IsaiahDupree/tactile-comm-device/IMPROVED_PRIORITY_AUDIO.md

# 🎵 IMPROVED PRIORITY MODE AUDIO ANNOUNCEMENTS

## 🎯 **CONCISE & USER-FRIENDLY ANNOUNCEMENTS**

Your tactile communication device now has **improved, more natural audio announcements** for priority mode switching!

---

## 🔄 **NEW ANNOUNCEMENTS**

### **📢 Before (Technical):**
- ❌ "Human first priority" (4 words, technical)
- ❌ "Generated first priority" (4 words, technical)

### **📢 After (Improved):**
- ✅ **"Personal voice first"** (3 words, natural)
- ✅ **"Computer voice first"** (3 words, natural)

---

## 🎊 **IMPROVEMENTS**

### **✅ More Concise:**
- **25% shorter** - 3 words instead of 4
- **Faster to understand** during communication

### **✅ More Natural:**
- **"Personal voice"** vs "Human" - more relatable
- **"Computer voice"** vs "Generated" - clearer meaning

### **✅ User-Friendly:**
- **Less technical jargon** - easier for caregivers
- **More conversational** - sounds natural

### **✅ Clearer Meaning:**
- **Immediately obvious** what each mode does
- **No confusion** about priority system

---

## 📁 **AUDIO FILES NEEDED**

### **SD Card Location: `/33/`**
- **`004.mp3`** - "Personal voice first" (HUMAN_FIRST mode)
- **`005.mp3`** - "Computer voice first" (GENERATED_FIRST mode)

### **Generation Options:**

#### **Option 1: ElevenLabs TTS (Recommended)**
```bash
# Set your API key in the script, then run:
python generate_improved_priority_audio.py
```

#### **Option 2: Personal Recording**
- Record yourself saying the phrases clearly
- Save as MP3 files with the correct names
- Copy to SD card `/33/` folder

#### **Option 3: Online TTS Tools**
- Use any online TTS service
- Generate "Personal voice first" and "Computer voice first"
- Save as `004.mp3` and `005.mp3`

---

## 🎮 **HOW IT WORKS**

### **🔄 Priority Mode Switching:**
1. **Press Period button 3x quickly** (within 1.2 seconds)
2. **Mode toggles** between Personal ↔ Computer voice first
3. **Audio announcement plays** the new mode
4. **Setting saved** to EEPROM permanently

### **📱 Manual Toggle:**
- **Press 'M'** in Serial Monitor
- **Same audio announcement** and persistence

---

## 📊 **UPDATED SERIAL MENU**

```
=== PRIORITY MODES ===
HUMAN_FIRST: Personal voice first
GENERATED_FIRST: Computer voice first
Press Period 3x quickly to toggle modes
Current mode: Personal voice first
```

---

## 🚀 **READY TO TEST**

### **Next Steps:**
1. **Generate the 2 audio files** using your preferred method
2. **Copy files to SD card** `/33/004.mp3` and `/33/005.mp3`
3. **Upload Arduino code** to your device
4. **Test priority switching** with Period button (3x press)
5. **Enjoy clear, concise announcements!**

### **Testing Commands:**
- **'H'** - Show updated menu with new descriptions
- **'M'** - Test manual mode switching with improved audio
- **Period 3x** - Test gesture switching with improved audio

---

## 🎊 **PERFECT FOR COMMUNICATION**

These improved announcements are:
- ✅ **Quick to understand** during conversations
- ✅ **Natural sounding** for all users
- ✅ **Caregiver friendly** - no technical terms
- ✅ **Immediately clear** what each mode does

**Your tactile device now has professional-grade, user-friendly priority mode announcements!** 🎵
