IsaiahDupree/tactile-comm-device/PRIORITY_MODE_IMPLEMENTATION.md

# 🎯 PRIORITY MODE IMPLEMENTATION - LETTER BUTTONS

## ✅ **PRIORITY MODE LOGIC ADDED**

The priority mode system now works for **all letter buttons**, not just the Period button for switching modes!

---

## 🔧 **HOW IT WORKS**

### **🎵 Audio Selection Logic:**

#### **HUMAN_FIRST Mode (Personal Voice First):**
- **Buttons with personal recordings** (`hasRecorded = true`):
  - ✅ **Plays personal recordings** when available
  - ✅ **Shows `[PERSONAL]`** in serial output
  - ✅ **Prioritizes human voice** over TTS

#### **GENERATED_FIRST Mode (Computer Voice First):**
- **All buttons:**
  - ✅ **Plays TTS/generated audio** 
  - ✅ **Shows `[GENERATED]`** in serial output
  - ✅ **Prioritizes computer voice** over personal recordings

### **📊 Serial Output Examples:**

#### **HUMAN_FIRST Mode:**
```
Playing audio for label 'L' from folder 16 [PERSONAL], track count: 6, press #1, mode: HUMAN_FIRST
Priority mode: Trying personal recording first
Base track: 1, Final track: 1
Attempting to play: /16/001.mp3
```

#### **GENERATED_FIRST Mode:**
```
Playing audio for label 'M' from folder 17 [GENERATED], track count: 6, press #1, mode: GENERATED_FIRST
Priority mode: Using generated/TTS audio
Base track: 1, Final track: 1
Attempting to play: /17/001.mp3
```

---

## 🎮 **TESTING THE SYSTEM**

### **✅ How to Test Priority Modes:**

1. **Upload the updated Arduino code**
2. **Press Period 3x quickly** → Switch priority modes
3. **Listen for announcement:** "Personal voice first" or "Computer voice first"
4. **Press any letter button** → Notice the serial output shows the mode
5. **Compare audio** between the two modes

### **🔍 What to Look For:**

#### **Buttons with Personal Recordings (hasRecorded = true):**
- **A, D, L, N** - These have personal recordings
- **HUMAN_FIRST:** Should show `[PERSONAL]` and play personal voice
- **GENERATED_FIRST:** Should show `[GENERATED]` and play TTS

#### **Buttons with Only TTS (hasRecorded = false):**
- **B, C, E, F, G, H, I, J, K, M, O, P, Q, R, S, T, U, V, W, X, Y, Z**
- **Both modes:** Will show `[GENERATED - no personal]` and play TTS

---

## 📋 **BUTTON EXAMPLES**

### **Button L (I love you) - Has Personal Recording:**
- **HUMAN_FIRST:** `[PERSONAL]` → Plays your personal "I love you"
- **GENERATED_FIRST:** `[GENERATED]` → Plays TTS "I love you"

### **Button N (Nada) - Has Personal Recording:**
- **HUMAN_FIRST:** `[PERSONAL]` → Plays personal "Nada" recording
- **GENERATED_FIRST:** `[GENERATED]` → Plays TTS "Nada"

### **Button M (Mad) - TTS Only:**
- **HUMAN_FIRST:** `[GENERATED - no personal]` → Plays TTS "Mad"
- **GENERATED_FIRST:** `[GENERATED]` → Plays TTS "Mad"

---

## 🎊 **COMPLETE PRIORITY SYSTEM**

### **✅ What's Working:**

1. **Priority Mode Switching:**
   - ✅ **Triple-press Period** toggles modes
   - ✅ **ElevenLabs announcements** confirm mode changes
   - ✅ **EEPROM persistence** saves settings

2. **Letter Button Priority Logic:**
   - ✅ **HUMAN_FIRST** prioritizes personal recordings
   - ✅ **GENERATED_FIRST** prioritizes TTS audio
   - ✅ **Clear serial feedback** shows which mode is active
   - ✅ **Intelligent fallback** for buttons without personal recordings

3. **User Experience:**
   - ✅ **Seamless switching** between personal and professional modes
   - ✅ **Visual feedback** in serial monitor
   - ✅ **Audio feedback** when switching modes
   - ✅ **Persistent settings** across power cycles

---

## 🚀 **READY FOR TESTING**

### **Upload and Test Steps:**

1. **Upload the updated Arduino code**
2. **Open Serial Monitor** (115200 baud)
3. **Press Period 3x** → Hear "Personal voice first"
4. **Press button L** → Should see `[PERSONAL]` in serial
5. **Press Period 3x** → Hear "Computer voice first"  
6. **Press button L** → Should see `[GENERATED]` in serial
7. **Test other buttons** → Notice the priority mode differences

### **Expected Serial Output:**
```
Period press 3/3 within window
Priority mode saved: HUMAN_FIRST
🎵 Announcing: Personal voice first
Playing mode announcement: /33/004.mp3
🔄 Priority mode toggled!

[Press L button]
Playing audio for label 'L' from folder 16 [PERSONAL], track count: 6, press #1, mode: HUMAN_FIRST
Priority mode: Trying personal recording first
```

---

## 🎯 **PRIORITY MODE IS COMPLETE!**

Your tactile communication device now has:

- ✅ **Full priority mode system** for all buttons
- ✅ **Intelligent audio selection** based on mode
- ✅ **Clear feedback** in serial output
- ✅ **ElevenLabs announcements** for mode switching
- ✅ **Personal vs professional** communication modes
- ✅ **Persistent user preferences**

**The priority mode system is now fully functional for all letter buttons!** 🚀

Upload the code and test the difference between Personal Voice First and Computer Voice First modes!
