IsaiahDupree/tactile-comm-device/PRIORITY_MODE_INTEGRATION_COMPLETE.md

# ✅ PRIORITY MODE INTEGRATION COMPLETE!

## 🎉 **TACTILE DEVICE FULLY ENHANCED**

Your tactile communication device now has **complete priority mode integration** with the existing codebase!

---

## ✅ **INTEGRATION COMPLETED**

### ✅ **Complete Integration:**

1. **🔧 EEPROM library added** for persistent storage
2. **🎯 Priority mode variables** added to global scope  
3. **🚀 loadPriorityMode()** integrated into existing setup()
4. **🔄 finalizePeriodWindow()** integrated into existing loop()
5. **🎮 Period triple-press detection** integrated into handlePress()
6. **📱 'M' command** added to existing serial handler
7. **📋 Priority mode info** added to existing printMenu()
8. **🎵 Audio playback functions** fixed to use existing VS1053 system

### **🎯 No Duplicate Functions:**
- ✅ **Used existing setup()** function - no duplication
- ✅ **Used existing loop()** function - no duplication  
- ✅ **Used existing handlePress()** function - enhanced
- ✅ **Used existing printMenu()** function - enhanced
- ✅ **Used existing serial commands** - added 'M' command

---

## 🎮 **HOW IT WORKS**

### **🔄 Priority Mode Switching:**
1. **Press Period button 3 times** within 1.2 seconds
2. **handlePress()** detects Period button and calls **handlePeriodPress()**
3. **Triple-press detection** counts presses within time window
4. **Mode toggles** between HUMAN_FIRST ↔ GENERATED_FIRST
5. **Audio announcement** plays the new mode
6. **EEPROM saves** the setting permanently

### **📱 Manual Mode Toggle:**
- **Press 'M'** in Serial Monitor to toggle modes manually
- **Same audio announcement** and EEPROM save as triple-press

### **💾 Persistent Storage:**
- **Mode saved** to EEPROM address 0
- **Loaded on startup** via loadPriorityMode() in setup()
- **Survives power cycles** and resets

---

## 🎵 **AUDIO SYSTEM**

### **🔊 Mode Announcements:**
- **`/33/004.mp3`** - "Human first priority" 
- **`/33/005.mp3`** - "Generated first priority"
- **Uses existing VS1053** audio playback system
- **Stops current audio** before playing announcement

### **🎧 Audio Priority Logic:**
- **HUMAN_FIRST:** Personal recordings → TTS fallback
- **GENERATED_FIRST:** TTS → Personal recordings fallback
- **Seamless integration** with existing audio mapping system

---

## 📊 **COMPLETE SYSTEM STATUS**

### **✅ Arduino Code Ready:**
- **120+ words** across all buttons
- **Priority mode system** fully integrated
- **No compilation errors** (except EEPROM.h lint in IDE)
- **Compatible with Arduino UNO R4 WiFi**

### **✅ SD Card Ready:**
- **84 TTS audio files** generated and copied
- **All folders 05-30** populated with expanded words
- **Existing personal recordings** preserved
- **SHIFT help system** ready for mode announcements

### **📝 Still Needed:**
- **2 mode announcement files:** `/33/004.mp3` and `/33/005.mp3`
- **16 personal recordings** for family names (optional)

---

## 🚀 **READY TO UPLOAD!**

### **Upload Process:**
1. **Connect Arduino UNO R4 WiFi** to computer
2. **Open Arduino IDE** and select board
3. **Upload tactile_communicator_vs1053.ino**
4. **Open Serial Monitor** (115200 baud)
5. **Test the system!**

### **Testing Steps:**
1. **Press 'H'** to see updated menu with priority modes
2. **Press 'M'** to test manual mode toggling
3. **Press Period 3x quickly** to test triple-press detection
4. **Press other buttons** to test normal operation
5. **Verify mode persists** after power cycle

---

## 📱 **SERIAL COMMANDS**

```
=== TACTILE COMMUNICATION DEVICE (VS1053) ===
C → Enter Calibration mode
E → Exit Calibration mode  
L → Load config from SD (config.csv)
S → Save config to SD (config.csv)
P → Print current mappings
M → Toggle priority mode manually
T → Test all buttons
+ → Volume up, - → Volume down, 1-9 → Set level
X → Stop current playback
H → Show this menu

=== PRIORITY MODES ===
HUMAN_FIRST: Personal recordings play first
GENERATED_FIRST: TTS audio plays first
Press Period 3x quickly to toggle modes
Current mode: HUMAN_FIRST

Press buttons to communicate!
```

---

## 🎊 **CONGRATULATIONS!**

Your tactile communication device now features:

- ✅ **120+ comprehensive vocabulary**
- ✅ **Dual priority modes** with smart switching
- ✅ **Triple-press gesture** for mode changes
- ✅ **Audio announcements** for feedback
- ✅ **Persistent settings** across power cycles
- ✅ **Professional integration** with existing code
- ✅ **No code duplication** or conflicts
- ✅ **Arduino UNO R4 WiFi ready**

**The integration is complete and ready for upload!** 🚀

Upload the code, generate the 2 mode announcement files, and enjoy your dramatically enhanced tactile communication system!
