IsaiahDupree/tactile-comm-device/PRIORITY_MODE_SYSTEM_ADDED.md

# ✅ PRIORITY MODE SYSTEM ADDED TO TACTILE DEVICE

## 🎉 **NEW FEATURE: DUAL PRIORITY MODES**

Your tactile communication device now has **two priority modes** that can be switched by pressing the **Period button 3 times quickly**!

---

## 🔄 **TWO PRIORITY MODES**

### **1. HUMAN_FIRST Mode (Default)**
- **Personal recordings** play first
- **TTS audio** plays as fallback
- **Best for familiar words** and personal expressions
- **Example:** "I love you" → Personal recording first, then TTS

### **2. GENERATED_FIRST Mode**  
- **TTS audio** plays first
- **Personal recordings** play as fallback
- **Best for consistent pronunciation** and new words
- **Example:** "Medicine" → TTS first, then personal recording

---

## 🎯 **HOW TO SWITCH MODES**

### **Triple-Press Period Button:**
1. **Press Period button 3 times** within 1.2 seconds
2. **Device announces** the new mode aloud
3. **Mode is saved** to EEPROM (survives power cycles)
4. **Normal Period function** still works with single/double press

### **Audio Announcements:**
- **"Human first priority"** - when switching to HUMAN_FIRST
- **"Generated first priority"** - when switching to GENERATED_FIRST

---

## 🛠️ **TECHNICAL IMPLEMENTATION**

### **Arduino Code Changes:**
- ✅ **EEPROM.h library** added for persistent storage
- ✅ **PriorityMode enum** with HUMAN_FIRST/GENERATED_FIRST
- ✅ **Triple-press detection** with 1.2-second window
- ✅ **Mode persistence** across power cycles
- ✅ **Audio announcements** for mode changes
- ✅ **Setup() integration** loads saved mode on startup
- ✅ **Loop() integration** handles period window finalization

### **New Functions Added:**
```cpp
void loadPriorityMode()        // Load mode from EEPROM
void savePriorityMode()        // Save mode to EEPROM  
void announcePriorityMode()    // Play mode announcement
void handlePeriodPress()       // Handle triple-press detection
void finalizePeriodWindow()    // Finalize single/double press
```

### **Audio Files Needed:**
- **`/33/004.mp3`** - "Human first priority" announcement
- **`/33/005.mp3`** - "Generated first priority" announcement

---

## 🎵 **AUDIO FILE LOCATIONS**

The priority mode announcements use the **SHIFT folder (33)** for system messages:

```
SD Card Structure:
/33/001.mp3 - Personal greeting (existing)
/33/002.mp3 - Device instructions (existing)  
/33/003.mp3 - Word mapping guide (existing)
/33/004.mp3 - "Human first priority" (NEW)
/33/005.mp3 - "Generated first priority" (NEW)
```

---

## 🚀 **USAGE SCENARIOS**

### **When to Use HUMAN_FIRST Mode:**
- ✅ **Family conversations** - personal names and expressions
- ✅ **Emotional communication** - "I love you", personal greetings
- ✅ **Familiar daily words** - names, personal preferences
- ✅ **When consistency with family voice is important**

### **When to Use GENERATED_FIRST Mode:**
- ✅ **Medical appointments** - consistent pronunciation of medications
- ✅ **Public settings** - clear, professional speech
- ✅ **New vocabulary** - words without personal recordings yet
- ✅ **When clarity and pronunciation are priority**

---

## 📱 **USER INTERFACE**

### **Serial Console Messages:**
```
🎉 System ready! Press buttons to communicate.
Current priority mode: HUMAN_FIRST
Press Period 3 times quickly to toggle priority mode.

Period press 1/3 within window
Period press 2/3 within window  
Period press 3/3 within window
🔄 Priority mode toggled!
Priority mode saved: GENERATED_FIRST
🎵 Announcing: Generated first priority
```

### **Status Indicators:**
- **Startup message** shows current mode
- **Console logging** for triple-press detection
- **Audio confirmation** when mode changes
- **EEPROM persistence** message on save/load

---

## 🎯 **NEXT STEPS TO COMPLETE**

### **1. Generate Audio Files**
- Record or generate "Human first priority" → `/33/004.mp3`
- Record or generate "Generated first priority" → `/33/005.mp3`

### **2. Copy to SD Card**
- Copy new audio files to SD card `/33/` folder
- Ensure existing SHIFT help files remain intact

### **3. Upload Arduino Code**
- Upload the updated `.ino` file with priority mode system
- Arduino UNO R4 WiFi fully compatible

### **4. Test the System**
- Test Period triple-press mode switching
- Verify audio announcements play correctly
- Test that normal Period function still works
- Confirm mode persists after power cycle

---

## 🎊 **CONGRATULATIONS!**

Your tactile communication device now has:
- ✅ **120+ words** across all buttons
- ✅ **Dual priority modes** for flexible communication
- ✅ **Smart mode switching** with triple-press gesture
- ✅ **Audio feedback** for mode changes
- ✅ **Persistent settings** that survive power cycles
- ✅ **Enhanced user experience** for different scenarios

**This makes your device incredibly versatile for both personal and professional communication needs!** 🚀
