IsaiahDupree/tactile-comm-device/SD_CARD_UPDATED.md

# ✅ SD CARD UPDATED - PRIORITY MODE READY!

## 🎉 **SD CARD SUCCESSFULLY UPDATED**

Your SD card now has **all the priority mode audio files** needed for the enhanced tactile communication device!

---

## 📁 **SD CARD CONTENTS: `/33/` FOLDER**

### **✅ Complete File List:**
```
E:\33\
├── 001.mp3     (19,035 bytes)  - SHIFT Help: Personal greeting
├── 002.mp3    (676,720 bytes)  - SHIFT Help: Device instructions  
├── 003.mp3  (1,247,653 bytes)  - SHIFT Help: Detailed help
├── 004.mp3     (37,659 bytes)  - 🆕 "Personal voice first"
├── 005.mp3     (36,823 bytes)  - 🆕 "Computer voice first"
└── README.txt      (257 bytes)  - Documentation
```

### **🆕 NEW PRIORITY MODE FILES:**
- **`004.mp3`** - **"Personal voice first"** (HUMAN_FIRST mode)
- **`005.mp3`** - **"Computer voice first"** (GENERATED_FIRST mode)

---

## 🎵 **AUDIO QUALITY**

### **✅ Generated with Windows TTS:**
- **Clear, natural speech** using Windows built-in voice
- **Optimized for communication** - concise and understandable
- **MP3 format** - compatible with VS1053 codec
- **128kbps bitrate** - good quality, small file size

### **🎯 Improved Announcements:**
- **More concise:** 3 words instead of 4+ words
- **More natural:** "Personal voice" vs "Human"
- **Clearer meaning:** "Computer voice" vs "Generated"
- **User-friendly:** No technical jargon

---

## 🎮 **HOW IT WORKS NOW**

### **🔄 Priority Mode Switching:**
1. **Press Period button 3 times** within 1.2 seconds
2. **Device announces:** "Personal voice first" or "Computer voice first"
3. **Mode toggles** between the two priority systems
4. **Setting saved** to EEPROM permanently

### **📱 Manual Toggle:**
- **Press 'M'** in Serial Monitor
- **Same audio announcement** plays
- **Same EEPROM persistence**

---

## 🚀 **READY TO UPLOAD & TEST**

### **✅ Complete System Status:**
- ✅ **Arduino code** - Priority mode fully integrated
- ✅ **SD card** - All audio files ready (120+ words + priority modes)
- ✅ **Audio announcements** - Clear, concise, user-friendly
- ✅ **EEPROM persistence** - Settings survive power cycles

### **🔧 Next Steps:**
1. **Upload Arduino code** to your Arduino UNO R4 WiFi
2. **Open Serial Monitor** (115200 baud)
3. **Test priority switching:**
   - Press Period 3x quickly
   - Listen for "Personal voice first" or "Computer voice first"
   - Press 'M' to test manual switching
4. **Test normal operation** - all 120+ words should work
5. **Verify persistence** - power cycle and check mode retention

---

## 📊 **TESTING COMMANDS**

### **Serial Monitor Commands:**
- **'H'** - Show menu with priority mode info
- **'M'** - Toggle priority mode manually (with audio)
- **'P'** - Print current button mappings
- **'T'** - Test all buttons

### **Physical Testing:**
- **Period 3x** - Toggle priority mode (with audio announcement)
- **Any button** - Test normal word playback
- **SHIFT button** - Test help system (includes new priority files)

---

## 🎊 **CONGRATULATIONS!**

Your tactile communication device now features:

- ✅ **120+ comprehensive vocabulary**
- ✅ **Dual priority modes** with audio announcements
- ✅ **Triple-press gesture control**
- ✅ **Clear, natural voice announcements**
- ✅ **Persistent settings** across power cycles
- ✅ **Professional user experience**

**The SD card is fully updated and ready for deployment!** 🚀

Upload your Arduino code and enjoy your dramatically enhanced tactile communication system with intelligent priority modes and crystal-clear audio feedback!
