IsaiahDupree/tactile-comm-device/TTS_UPDATE_COMPLETE_SUMMARY.md

# 🎵 TTS VOCABULARY UPDATE COMPLETE!

## ✅ **WHAT WE'VE ACCOMPLISHED:**

### **1. Console Logging Enhancement ✅**
- **Added `getAudioText()` function** to map audio files to their text content
- **Enhanced playback logging** to show exactly what words are being played
- **Example output:** `🎵 Playing: /23/002.mp3 -> "Sad"`

### **2. TTS Update Script Created ✅**
- **Complete vocabulary mapping** from your JSON specification
- **Smart personal recording detection** - won't overwrite Alari, Daddy, etc.
- **Voice ID configured:** `RILOU7YmBhvwJGDGjNmP` (previously used)
- **Ready to run** once you add your ElevenLabs API key

### **3. Audio Manifest Generated ✅**
- **Perfect track-to-text mapping** created at `E:\AUDIO_MANIFEST.json`
- **Shows exactly what each file contains:**
  - `/23/001.mp3` = "Susu" (personal recording)
  - `/23/002.mp3` = "Sad" (TTS)
  - `/23/003.mp3` = "Scarf" (TTS)
  - And so on...

### **4. Updated Arduino Code ✅**
- **Enhanced console logging** shows text content when playing audio
- **Two-bank priority system** fully supports your vocabulary
- **Smart bank selection** respects personal vs TTS priority

## 🎯 **EXPECTED CONSOLE OUTPUT:**

When you press the S button, you'll now see:
```
[BUTTON] PCF8575 #0 GPIO 7 → S [F:23/REC:1/TTS:7] | Press #1 @ 15234ms
Playing audio for label 'S' from folder 23 [REC:1/TTS:7], press #1, mode: HUMAN_FIRST
Priority mode: HUMAN_FIRST -> Selected RECORDED bank, track 1
🎵 Playing: /23/001.mp3 -> "Susu [REC]"
```

And for the second press:
```
🎵 Playing: /23/002.mp3 -> "Sad"
```

## 📋 **YOUR VOCABULARY MAPPING:**

**Personal Recordings (Protected):**
- A: Alari (`/05/001.mp3`)
- D: Daddy (`/08/001.mp3`)
- L: I love you (`/16/001.mp3`)
- N: Nada, Nadowie, Noah (`/18/001-003.mp3`)
- S: Susu (`/23/001.mp3`)

**TTS Words (Your JSON Vocabulary):**
- **A:** Amer, Apple, Arabic Show
- **B:** Bagel, Bathroom, Bed, Blanket, Breathe, Bye
- **C:** Call, Car, Chair, Coffee, Cold, Cucumber
- **D:** Deen, Doctor, Door, Down
- **F:** FaceTime, Funny
- **G:** Garage, Go, Good Morning
- **H:** Happy, Heartburn, Hot, How are you, Hungry
- **I:** Inside, iPad
- **K:** Kaiser, Kiyah, Kleenex, Kyan
- **L:** Lee, Light Down, Light Up
- **M:** Mad, Medical, Medicine, Meditate, Mohammad
- **N:** No
- **O:** Outside
- **P:** Pain, Phone
- **R:** Rest, Room
- **S:** Sad, Scarf, Shoes, Sinemet, Sleep, Socks, Stop
- **T:** TV, Togamet, Tylenol
- **U:** Up, Urgent Care
- **W:** Walk, Walker, Water, Wheelchair
- **Y:** Yes

## 🚀 **NEXT STEPS:**

### **To Generate TTS Files:**
1. **Add your ElevenLabs API key** to `update_vocabulary_tts.py`
2. **Run the script:** `python update_vocabulary_tts.py`
3. **Wait for generation** (~2-3 minutes for all files)

### **To Test Priority Mode:**
1. **Upload the updated Arduino code**
2. **Press S button once** → Should play "Susu" (personal) in HUMAN_FIRST mode
3. **Press S button twice** → Should play "Sad" (TTS)
4. **Triple-press Period** to switch modes
5. **Press S button once** → Should play "Sad" (TTS) in GENERATED_FIRST mode

## 🎵 **CONSOLE LOGGING BENEFITS:**

- **See exactly what's playing:** No more guessing which audio file is which
- **Debug priority mode:** Verify correct bank selection
- **Track personal recordings:** `[REC]` tag shows personal vs TTS
- **Troubleshoot issues:** Clear file path and content mapping

## ✅ **SYSTEM STATUS:**

- ✅ **SD Card:** Reorganized with proper REC/TTS banks
- ✅ **Arduino Code:** Enhanced with text logging and compilation fixes
- ✅ **Vocabulary:** Fully mapped to your JSON specification
- ✅ **TTS Script:** Ready to generate all missing audio files
- ✅ **Priority Mode:** Bulletproof two-bank system complete
- 🎯 **Ready for final testing!**

**Your tactile communication device now has comprehensive vocabulary support with crystal-clear console logging!** 🎯✨
