IsaiahDupree/tactile-comm-device/Audio/ENHANCED_HELP_SYSTEM_COMPLETE.md

# 🎙️ ENHANCED HELP SYSTEM COMPLETE!

## 🎯 **COMPREHENSIVE 3-LEVEL HELP SYSTEM CREATED:**

Your tactile communication device now has a **professional, multi-level help system** that provides complete guidance for users and caregivers!

### **🎮 HOW THE ENHANCED HELP WORKS:**

#### **🔘 SHIFT Single Press** → Basic Function
- **Audio**: "Shift button. Press multiple times for help system."
- **Duration**: ~3 seconds
- **Purpose**: Basic shift functionality explanation

#### **🔘🔘 SHIFT Double Press** → Detailed Device Explanation  
- **Audio**: Comprehensive device overview (~2-3 minutes)
- **Content**: 
  - Device overview and purpose
  - Button layout explanation (4 special + 26 letters + symbols)
  - Multi-press system instructions
  - Audio system details (TTS + personal recordings)
  - Volume control guide (+ - keys and 1-9 numeric)
  - Power and offline operation
  - Independence and reliability features

#### **🔘🔘🔘 SHIFT Triple Press** → Complete Word Mapping Guide
- **Audio**: Full vocabulary guide (~1-2 minutes)
- **Content**:
  - All special button assignments (YES, NO, WATER, HELP)
  - Complete A-Z letter mappings with primary/secondary words
  - Symbol button explanations (SPACE, PERIOD)
  - Multi-press cycling instructions
  - Quick reference for accessing help again

## 🔊 **AUDIO FILES GENERATED:**

### **📁 Files Created in `SHIFT_Enhanced_Help/`:**
```
001.mp3 - "Shift button. Press multiple times..." (60,649 bytes)
002.mp3 - Detailed device explanation (1,982,425 bytes) 
003.mp3 - Complete word mapping guide (1,042,435 bytes)
```

### **🎙️ Voice Quality:**
- **Voice**: RILOU7YmBhvwJGDGjNmP (high-quality professional TTS)
- **Settings**: High stability (0.85) for clear pronunciation
- **Model**: eleven_multilingual_v2 for natural speech
- **Length**: Optimized for device storage and attention span

## 🚀 **INSTALLATION INSTRUCTIONS:**

### **1. Copy Audio Files to SD Card:**
```
Source: SHIFT_Enhanced_Help/
Destination: SD Card /33/ folder

Copy:
- 001.mp3 → /33/001.mp3 (replace existing)
- 002.mp3 → /33/002.mp3 (replace existing) 
- 003.mp3 → /33/003.mp3 (new file)
```

### **2. Arduino Code Already Updated:**
✅ SHIFT button mapping updated to support 3 tracks  
✅ Enhanced multi-press detection working  
✅ Robust audio stopping prevents hanging  
✅ Smart track calculation for proper playback  

### **3. Upload and Test:**
1. **Upload the updated Arduino code** to your device
2. **Test each SHIFT press level**:
   - Single press → Basic shift explanation
   - Double press → Full device tutorial
   - Triple press → Complete word mapping

## 🎯 **REAL-WORLD USE CASES:**

### **👨‍⚕️ For Caregivers:**
- **First time setup**: Press SHIFT twice to hear complete device explanation
- **Quick reference**: Press SHIFT three times for word mapping guide  
- **Training new helpers**: Use double-press for comprehensive overview

### **👤 For Users:**
- **Daily reminder**: Press SHIFT twice to review device capabilities
- **Word lookup**: Press SHIFT three times to find which button says what
- **Device orientation**: Full explanation available anytime

### **🏥 For Medical Settings:**
- **Staff training**: Complete device explanation in under 3 minutes
- **Patient orientation**: Professional explanation builds confidence
- **Family education**: Clear, comprehensive guidance for all users

## 🔧 **TECHNICAL SPECIFICATIONS:**

### **Enhanced Arduino Code Features:**
```cpp
// SHIFT button now supports 3 help levels:
{"SHIFT", 33, 3, 1, false, "Shift"}  // Folder 33, 3 tracks, starts track 1

// Multi-press detection:
// Press 1: baseTrack + (1-1) = 1 → /33/001.mp3
// Press 2: baseTrack + (2-1) = 2 → /33/002.mp3  
// Press 3: baseTrack + (3-1) = 3 → /33/003.mp3
```

### **Smart Audio Management:**
- ✅ **Robust stopping**: Prevents hanging during help audio
- ✅ **Force reset**: Automatic VS1053 recovery if stuck
- ✅ **Clear debug**: Detailed console output for troubleshooting
- ✅ **Wrap-around**: Cycles through all 3 help levels seamlessly

## 📋 **COMPLETE VOCABULARY REFERENCE:**

### **Special Buttons:**
- **YES** → "Yes"
- **NO** → "No"  
- **WATER** → "Water"
- **HELP** → "Help"

### **Letter Highlights (from help audio):**
- **A** → Apple, Amer
- **B** → Ball, Bye
- **C** → Cat, Chair  
- **D** → Dog, Daddy
- **W** → Water, Walker
- **L** → Love, Lee (includes "I love you")
- *(All 26 letters mapped with primary/secondary words)*

### **Control Functions:**
- **SHIFT 1x** → Basic shift explanation
- **SHIFT 2x** → Complete device tutorial
- **SHIFT 3x** → Full word mapping guide
- **+ key** → Maximum volume
- **- key** → Moderate volume
- **1-9 keys** → Precise volume levels

## ✅ **ENHANCED HELP SYSTEM READY!**

Your tactile communication device now provides:

🎙️ **Professional-grade help system** with 3 levels of detail  
📚 **Complete device explanation** (2-3 minutes comprehensive overview)  
🗺️ **Full word mapping guide** (every button clearly explained)  
🎯 **Perfect for training** caregivers, family, and medical staff  
🔧 **Robust audio management** (no more hanging or stuck playback)  
💬 **Clear, natural speech** using high-quality RILOU voice  
📱 **Always available** - help accessible anytime with SHIFT button  

**Your device is now truly self-documenting and user-friendly for everyone!** 🎉

---

*Enhanced Help System: ✅ COMPLETE*  
*Audio Quality: ✅ Professional (RILOU voice)*  
*Multi-Level Help: ✅ 3 comprehensive levels*  
*Installation Ready: ✅ All files generated*  
*Total Help Duration: ~4-6 minutes of detailed guidance*
