IsaiahDupree/tactile-comm-device/Audio/FRESH_SD_CARD_COMPLETE.md

# Fresh SD Card Setup Complete! ✅

## NEW PRIORITY SYSTEM IMPLEMENTED

Your tactile communication device now has a **completely fresh SD card** with the **improved priority system**:

### 🎯 **New Priority System:**

1. **1st Press**: Generated TTS (clear, consistent, always available)
2. **2nd Press**: Personal Recorded Words (familiar voices, emotional connection)
3. **3rd+ Press**: Additional TTS words (extended vocabulary)

## 📁 **SD Card Structure Created**

✅ **57 TTS audio files generated** using ElevenLabs RILOU voice  
✅ **18 recorded words copied** to 2nd press positions  
✅ **Fresh folder structure** (01-33) with numbered files  
✅ **SHIFT help system** implemented  

## 🔧 **Arduino Code Updated**

The Arduino code now includes **detailed documentation** showing exactly what each button press will play:

```cpp
// A: 1=Apple[TTS], 2=Amer[REC], 3=Alari[REC], 4=Arabic[TTS], 5=Amory[REC]
{"A", 5, 5, true, "Apple"},

// B: 1=Ball[TTS], 2=Bye[REC], 3=Bathroom[TTS], 4=Bed[TTS]  
{"B", 6, 4, true, "Ball"},

// SHIFT with Help System: 1=Shift[TTS], 2=Device Help[TTS]
{"SHIFT", 33, 2, false, "Shift"}
```

## 🎙️ **SHIFT Double-Press Help System**

**Special Feature Implemented:** Press SHIFT twice quickly to hear:

> *"This is your tactile communication device. Press any button once for the main word, twice for personal recordings, or three times for additional options. Press SHIFT twice for help."*

## 📊 **Example Button Usage**

### Letter A:
- **Press 1**: "Apple" (TTS - clear, consistent)
- **Press 2**: "Amer" (Your recorded voice - personal, familiar)  
- **Press 3**: "Alari" (Your recorded voice)
- **Press 4**: "Arabic" (TTS)
- **Press 5**: "Amory" (Your recorded voice)

### Letter L:
- **Press 1**: "Love" (TTS)
- **Press 2**: "Lee" (Your recorded voice)
- **Press 3**: "I love you" (Your recorded voice) 
- **Press 4**: "Light" (TTS)

## ✅ **Ready for Testing**

1. **Upload the updated Arduino code** to your device
2. **Test the new priority system**:
   - Single press = TTS (always available)
   - Double press = Recorded words (personal touch)
3. **Test SHIFT double-press** for device help
4. **Enjoy the improved communication experience!**

## 🎵 **Audio Quality Summary**

- **Voice**: ElevenLabs RILOU (clear & understandable)
- **Total Files**: 57 TTS + 18 recorded = 75 audio files
- **File Format**: MP3, optimized for VS1053 codec
- **File Size**: Average 12-15KB per file
- **Multi-press Window**: 1000ms (1 second) for reliable detection

---

## 🚀 **Key Improvements from Fresh Setup**

### **✅ Better User Experience:**
- **Consistent first experience**: TTS always available on first press
- **Personal second experience**: Your voice for important words
- **Extended vocabulary**: Additional words on 3rd+ presses

### **✅ Clearer System Logic:**
- **Predictable**: Users know first press = TTS, second = personal
- **Documented**: Arduino code shows exactly what each press plays
- **Help system**: SHIFT double-press explains the device

### **✅ Technical Excellence:**
- **Clean slate**: Fresh SD card with proper structure
- **Proper naming**: Numbered files (001.mp3, 002.mp3, etc.)
- **Updated mappings**: Arduino code matches SD card exactly

---

**Your tactile communication device is now ready with the improved priority system! 🎉**

*Generated: 2025-08-01 20:52 EST*  
*SD Card: E:\ (Fresh Setup)*  
*Voice: RILOU (ElevenLabs)*  
*Priority: TTS First, Recorded Second*
