IsaiahDupree/tactile-comm-device/Audio/PRIORITY_AUDIO_SYSTEM_COMPLETE.md

# 🎉 Priority-Based Audio System Complete!

## **✅ System Successfully Updated**

Your tactile communicator now has a **revolutionary priority-based audio system** that provides:

### **🎯 Priority 1: Human Recorded Audio (Preserved)**
- **YES**, **NO**, **WATER** → Your personal recordings (highest priority)
- **A**, **B**, **D**, **K**, **L** → Personal names and words (Amer, Alari, Bye, Deen, Daddy, Kiyah, Kyan, Lee, I love you)
- **AUX**, **G**, **N**, **S**, **U**, **W** → Personal messages (Hello, Good Morning, Nadowie, Noah, Susu, Urgent Care, Walker, wheelchair)

### **🎯 Priority 2: Generated TTS Audio (Created)**
Just generated **15 new TTS audio files** for complete system coverage:

| Folder | Label | Generated Word | Purpose |
|---|---|---|---|
| 09 | E | "Elephant" | Simple E word |
| 11 | G | "Go" | Backup for Good Morning |
| 14 | J | "Jump" | New J word |
| 18 | N | "No" | Backup for Nada/Nadowie/Noah |
| 21 | Q | "Queen" | New Q word |
| 23 | S | "Sun" | Backup for Scarf/Susu/Sinemet |
| 25 | U | "Up" | Backup for Urgent Care |
| 26 | V | "Van" | New V word |
| 27 | W | "Water" | Backup for Walker/wheelchair |
| 28 | X | "X-ray" | New X word |
| 29 | Y | "Yellow" | New Y word |
| 30 | Z | "Zebra" | New Z word |
| 31 | SPACE | "Space" | Space button |
| 32 | PERIOD | "Period" | Period button |
| 33 | SHIFT | "Shift" | Shift button |

## **🔧 Technical Improvements**

### **Smart Label-Based Mapping:**
- ✅ **Button positions** can change freely
- ✅ **Audio always follows** the label
- ✅ **No more broken audio** from button remapping
- ✅ **Future-proof** system design

### **Enhanced Arduino Code:**
- ✅ **Priority indicators** in console logging (`[RECORDED]` vs `[GENERATED]`)
- ✅ **Smart fallback system** if files are missing
- ✅ **TTS suggestions** for missing audio
- ✅ **Multi-press cycling** for labels with multiple tracks
- ✅ **Detailed error reporting** with helpful symbols (✓ ⚠ ✗ ℹ ↳)

### **SD Card Organization:**
- ✅ **Complete folder coverage** (folders 01-33)
- ✅ **Backup preservation** (original files in `backup_original/`)
- ✅ **Consistent naming** (001.mp3, 002.mp3, etc.)
- ✅ **Documentation files** created

## **🎵 Your Current Button Mapping**

Based on your calibration:
- **Button 0** → **YES** (Folder 01) → *Your personal "Yes"*
- **Button 6** → **C** (Folder 07) → *Chair, car, Cucumber*
- **Button 20** → **WATER** (Folder 03) → *Your personal "Water"*
- **Button 23** → **L** (Folder 16) → *Lee, I love you, light*
- **Button 25** → **NO** (Folder 02) → *Your personal "No"*
- **Button 30** → **D** (Folder 08) → *Deen, Daddy, Doctor, Door*

## **🚀 What This Solves**

### **Before:**
- ❌ Audio tied to button positions
- ❌ Remapping broke audio associations
- ❌ Missing audio for many letters
- ❌ No fallback system

### **After:**
- ✅ Audio tied to **labels** (flexible)
- ✅ Button remapping **preserves** audio
- ✅ **Complete alphabet coverage**
- ✅ **Smart fallback** and priority system
- ✅ **Human recordings prioritized**
- ✅ **Generated audio** fills gaps

## **🎯 Next Steps**

1. **Upload to Arduino** and test button presses
2. **Verify audio playback** for all your calibrated buttons
3. **Test multi-press cycling** on buttons with multiple tracks
4. **Try calibration mode** to add new buttons
5. **Enjoy your complete tactile communication system!**

## **🛠️ System Benefits**

- **🔧 Maintainable**: Easy to add/modify without breaking existing mappings
- **📱 Consistent**: Same label always plays same audio
- **🔄 Flexible**: Button positions can change anytime
- **📈 Scalable**: Add new buttons/labels without restructuring
- **🎵 Complete**: Every letter has audio (recorded or generated)
- **🔒 Safe**: Original recordings preserved with backup system

---

**Your tactile communicator is now a complete, professional-grade assistive technology device!** 🌟
