IsaiahDupree/tactile-comm-device/Audio/SD_CARD_RECOVERY.md

# 🚨 SD CARD RECOVERY - DEVICE HANGING ISSUE

## **🔍 DIAGNOSIS:**
Your device is hanging on `SD.exists()` calls, which indicates **SD card corruption or file system issues**.

**Symptoms:**
```
✓ Audio playback started
[BUTTON] PCF8575 #0 GPIO 3 → A [F:5/T:5] | Press #1 @ 26844ms  
Playing audio for label 'A' from folder 5 [GENERATED], track count: 5, press #1
Base track: 1, Final track: 1
Attempting to play: /05/001.mp3
[DEVICE HANGS HERE - no further output]
```

## **🛠️ IMMEDIATE SOLUTIONS:**

### **1. 🚨 EMERGENCY SD CARD RECOVERY:**

#### **Step 1: Remove SD Card Safely**
- Power off your device completely
- Remove the SD card from the device
- Insert into your computer's SD card reader

#### **Step 2: Check SD Card Health**
```bash
# Windows: Check for errors
chkdsk E: /f /r

# Or use Windows Explorer:
# Right-click SD card → Properties → Tools → Check
```

#### **Step 3: Backup Current Files**
```bash
# Copy everything to backup before fixing
xcopy E:\*.* "C:\Users\Isaia\Documents\SD_Card_Backup\" /s /e /h
```

### **2. 📱 REFORMAT SD CARD (RECOMMENDED):**

#### **Option A: Quick Format (Recommended)**
1. **Right-click SD card** in Windows Explorer
2. **Format...** 
3. **File System: FAT32**
4. **Allocation Unit: Default**
5. **Quick Format: CHECKED**
6. **Click Start**

#### **Option B: Full Format (If Quick Fails)**
1. Same as above but **UNCHECK Quick Format**
2. ⚠️ This takes much longer but fixes deeper corruption

### **3. 🔄 RESTORE FILES TO FRESH SD CARD:**

Run the SD card update script on the freshly formatted card:
```bash
cd "C:\Users\Isaia\Documents\3D Printing\Projects\Button\Audio"
python update_sd_card_help_system.py
```

## **🔧 LONG-TERM PREVENTION:**

### **A. Use Higher Quality SD Card**
- **Class 10 or better** for reliable performance
- **Brand name cards** (SanDisk, Samsung, Kingston)
- **32GB max** for best Arduino compatibility

### **B. Proper Power Management**
- Always **power off device** before removing SD card
- Use **proper shutdown sequence** to prevent corruption
- Avoid **sudden power loss** during file operations

### **C. Regular Backups**
```bash
# Weekly backup script
xcopy E:\*.* "C:\Users\Isaia\Documents\Weekly_SD_Backup_%date%" /s /e /h
```

## **🎯 IMMEDIATE TESTING STEPS:**

### **After SD Card Recovery:**
1. **Reinsert fresh SD card** into device
2. **Power on device** and test basic functions
3. **Test SHIFT button** (should work with new help files)
4. **Test A button** (should work without hanging)
5. **Test audio interruption**: Press SHIFT, then immediately press A

### **Expected Behavior:**
```
✓ Audio playback started
[BUTTON] PCF8575 #0 GPIO 3 → A [F:5/T:5] | Press #1 @ 26844ms
Playing audio for label 'A' from folder 5 [GENERATED], track count: 5, press #1
Base track: 1, Final track: 1
Attempting to play: /05/001.mp3
[DEBUG] About to check if file exists...
[DEBUG] Calling SD.exists()...
[DEBUG] SD.exists() returned: TRUE
Stopping current audio...
Audio stopped successfully
Starting new audio...
✓ Audio playback started
```

## **🚨 IF PROBLEMS PERSIST:**

### **Hardware Issues:**
- **SD card reader on device may be faulty**
- **Power supply issues** causing SD corruption
- **Wiring problems** to SD card module

### **Alternative Solutions:**
1. **Try different SD card** to isolate hardware issues
2. **Check power supply voltage** (should be stable 5V)
3. **Verify SD card wiring** connections are solid
4. **Consider SD card module replacement** if all else fails

## **📋 SUCCESS CHECKLIST:**

✅ SD card formatted successfully (FAT32)  
✅ All audio files copied to fresh card  
✅ Device boots without hanging  
✅ SHIFT help system works (1x, 2x, 3x presses)  
✅ All letter buttons play audio without hanging  
✅ Audio interruption works smoothly  
✅ No more "file not found" errors for existing files  

---

**💡 ROOT CAUSE:** SD card file system corruption causing `SD.exists()` calls to hang the Arduino. Fresh formatting resolves file system integrity issues.

**🎯 EXPECTED OUTCOME:** Device will work flawlessly with reliable audio playback and smooth button transitions after SD card recovery.
