IsaiahDupree/tactile-comm-device/Audio/SHIFT_BUTTON_UPDATE.md

# SHIFT Button Enhanced Update

## ✅ **COMPLETED CHANGES:**

### **🎯 New SHIFT Button Layout (Improved User Experience)**

| **Press** | **File** | **Content** | **Source** | **Duration** |
|---|---|---|---|---|
| **1x** | `001.mp3` | "Hello How are You" | **Personal Recording** | ~3 sec |
| **2x** | `002.mp3` | Device Instructions | TTS (Normal Speed) | ~2 min |
| **3x** | `003.mp3` | **Slower** Word List Mapping | TTS (Slow Speech) | ~4 min |

### **🎙️ Key Improvements Made:**

#### **1. Personal Touch (Press 1x):**
- ✅ **Replaced TTS** with your **personal recorded greeting**
- ✅ **Warmer, more familiar** voice for first interaction
- ✅ **Perfect introduction** for new users and caregivers

#### **2. Better Comprehension (Press 3x):**
- ✅ **SLOWER speech** for word list mapping
- ✅ **Clearer pauses** between letters and words
- ✅ **Enhanced TTS settings**:
  - Stability: 0.95 (maximum clarity)
  - Similarity: 0.85 (consistent voice)
  - Style: 0.05 (minimal for clarity)
- ✅ **Better phrasing**: "Letter A has: Apple, Amer..." (clearer structure)

### **📊 File Details:**

```
E:\33\001.mp3 → 58,559 bytes   (Personal recording)
E:\33\002.mp3 → 676,720 bytes  (TTS instructions)
E:\33\003.mp3 → 1,247,653 bytes (SLOW TTS word mapping)
```

### **🎮 How It Works Now:**

#### **SHIFT Press 1x** → Personal Greeting
- **Your recorded voice** saying "Hello How are You"
- **Immediate familiarity** for users
- **Perfect ice-breaker** for new interactions

#### **SHIFT Press 2x** → Device Instructions
- Complete device overview (normal TTS speed)
- Explains buttons, multi-press, offline operation
- **Ideal for caregiver training**

#### **SHIFT Press 3x** → Slower Word List
- **Every button mapped clearly**: "Letter A has: Apple, Amer, Alari..."
- **Slower, more deliberate speech** for easy following
- **Longer pauses** between sections
- **Perfect reference** for finding specific words

### **🚀 Benefits:**

- ✅ **Personal connection** through recorded greeting
- ✅ **Easier comprehension** with slower word mapping
- ✅ **Professional training** with structured instructions
- ✅ **Complete accessibility** for all user levels
- ✅ **Familiar voice** creates comfort and trust

### **🎯 Next Steps:**

1. **Insert SD card** back into device
2. **Test all three SHIFT levels**:
   - Press 1x → Hear your personal greeting
   - Press 2x → Hear device instructions  
   - Press 3x → Hear slower word mapping
3. **Train caregivers** using the structured help system
4. **Enjoy enhanced user experience** with personal touch!

---

**Your tactile communication device now has a perfect balance of personal warmth and professional functionality!** 🎉
