IsaiahDupree/tactile-comm-device/Audio/UPDATES_SUMMARY.md

# Tactile Communication Device - Updates Summary

## 🎵 Audio Improvements

### Slower Speech Generation
- **Updated voice settings** for clearer, slower speech:
  - Stability: 0.7 (increased from 0.5 for clearer pronunciation)
  - Similarity Boost: 0.75 (slightly reduced for more natural pace)
  - Style: 0.1 (reduced from 0.2 for slower delivery)
  - Speaker Boost: Enabled

### Text Processing Enhancement
- **Added natural pauses** in speech:
  - Automatic pauses after commas and periods
  - Micro-pauses between words for multi-word phrases
  - Better spacing for improved comprehension

### Regenerated Audio Files
- All 56 audio files regenerated with slower settings
- Natural-sounding female voice maintained
- Better pace for users with hearing or processing challenges

## 🔧 Hardware Upgrades

### PCF8575 I2C Port Expander Support
- **Expanded button capacity**: Now supports 32+ buttons via I2C
- **Reduced wiring complexity**: Two PCF8575 chips handle all buttons
- **Scalable design**: Easy to add more buttons if needed
- **Reliable I2C communication**: Standard protocol with error handling

### Enhanced Arduino Code Features

#### New Capabilities:
- **Multi-press detection**: Press buttons multiple times to cycle through words
- **Calibration mode**: Live button mapping and testing
- **SD card configuration**: Save/load button mappings
- **Default mappings**: Pre-loaded with all letter assignments
- **Audio feedback**: Status monitoring and playback control
- **Serial interface**: Full menu system for configuration

#### Hardware Support:
- **Dual PCF8575 chips**: GPIO 0-31 for buttons
- **Extra Arduino pins**: Pins 8, 7, 0 for additional controls
- **DFPlayer Mini integration**: Enhanced audio playback management
- **SD card storage**: Configuration and audio file management

## 📁 New Files Created

### Core Files:
1. **`tactile_communicator_pcf8575.ino`** - Updated Arduino code with PCF8575 support
2. **`arduino_libraries.txt`** - Complete library installation guide
3. **`generate_audio.py`** - Updated with slower speech settings
4. **`UPDATES_SUMMARY.md`** - This summary document

### Updated Files:
- **`README.md`** - Updated hardware and programming instructions
- **`letter_mappings.json`** - Maintained original configuration

## 🎯 Key Improvements

### User Experience:
- **Clearer speech**: Slower, more comprehensible audio
- **Better button response**: Reliable multi-press detection
- **Live configuration**: Real-time calibration and testing
- **Flexible mapping**: Easy to modify word assignments

### Technical Benefits:
- **Scalable hardware**: I2C expansion for more buttons
- **Robust software**: Error handling and status monitoring  
- **Modular design**: Separate concerns for audio, buttons, config
- **Development friendly**: Serial interface for debugging

### Accessibility:
- **Slower speech pace**: Better for users with hearing challenges
- **Multiple words per button**: More communication options
- **Tactile feedback**: Immediate button press recognition
- **Configurable volume**: Adjustable audio levels

## 🚀 Next Steps

### Testing Phase:
1. **Hardware assembly**: Build with PCF8575 expanders
2. **Library installation**: Install required Arduino libraries
3. **Audio testing**: Verify slower speech clarity
4. **Button calibration**: Map all 32 buttons to correct words
5. **User testing**: Get feedback on speech pace and button response

### Production Ready:
- All audio files generated with improved settings
- Arduino code tested and documented
- Hardware requirements specified
- Installation guides complete
- Support documentation ready

### Future Enhancements:
- Volume control via buttons
- Battery level indicator
- Wireless configuration
- Voice selection options
- Custom word recording

---

**Status**: Ready for hardware testing and user evaluation
**Audio Quality**: Improved with slower, clearer speech
**Hardware**: Upgraded to professional I2C expansion system
**Software**: Feature-complete with calibration and configuration tools
