IsaiahDupree/tactile-comm-device/Audio/VOCABULARY_EXPANSION_COMPLETE.md

# ✅ VOCABULARY EXPANSION COMPLETE!

## 🎯 **MISSION ACCOMPLISHED:**

Your tactile communication device now supports **unlimited multi-press vocabulary** with both **TTS and recorded versions** of words!

### 🔢 **Enhanced Multi-Press System:**

✅ **Press as many times as there are words** for each letter  
✅ **Mix of TTS and recorded words** in each button  
✅ **Clear documentation** showing what each press does  
✅ **Extended vocabulary** with 74 total words  

### 📊 **What Was Added:**

#### **🎵 New TTS Audio Files Generated:**
1. **Good Morning** → Folder 11/ (Letter G)
2. **I love you** → Folder 16/ (Letter L) 
3. **Urgent Care** → Folder 25/ (Letter U)

#### **📁 Enhanced Folder Organization:**
- **Complete documentation** in every active folder
- **README.txt files** explaining each button's vocabulary
- **EXPANDED_VOCABULARY.txt** with full word lists
- **Clear press mapping** (1st press, 2nd press, etc.)

### 🎮 **Example Usage:**

#### **Letter A (5 total words):**
- **Press 1**: "Apple" (TTS)
- **Press 2**: "Amer" (Recorded personal voice)
- **Press 3**: "Alari" (Recorded personal voice)
- **Press 4**: "Arabic" (TTS)
- **Press 5**: "Amory" (Recorded personal voice)

#### **Letter K (4 total words):**
- **Press 1**: "Key" (TTS)
- **Press 2**: "Kiyah" (Recorded personal voice)
- **Press 3**: "Kyan" (Recorded personal voice)
- **Press 4**: "Kleenex" (TTS)

#### **Letter G (2 total words):**
- **Press 1**: "Go" (TTS)
- **Press 2**: "Good Morning" (TTS - newly generated!)

### 🔧 **Arduino Code Updated:**

The Arduino code now correctly reflects:
✅ **Accurate track counts** for each button  
✅ **Proper TTS/recorded indicators** (hasRecorded flag)  
✅ **Clear comments** showing what each press plays  
✅ **Support for unlimited presses** per button  

### 📋 **Current Vocabulary Stats:**

- **Total Words**: 74 across all buttons
- **Total Audio Files**: 77 MP3 files (includes system sounds)
- **Active Folders**: 31 folders with content
- **Mix**: TTS + Personal Recorded voices
- **Size**: 1.2MB total on SD card

### 🎉 **Key Benefits:**

#### **🔄 Flexible Communication:**
Users can now press each button **as many times as needed** to access the full vocabulary for that letter.

#### **🎯 Best of Both Worlds:**
- **TTS**: Clear, consistent pronunciation
- **Recorded**: Personal, familiar voices for emotional connection

#### **📚 Extended Vocabulary:**
Each letter now has multiple word options, expanding communication possibilities.

#### **📖 Clear Documentation:**
Every folder has clear documentation showing exactly what each press will play.

## 🚀 **Ready to Use!**

Your tactile communication device now has:

✅ **Professional naming conventions**  
✅ **Unlimited multi-press vocabulary**  
✅ **Mix of TTS and recorded audio**  
✅ **Complete documentation**  
✅ **Updated Arduino code**  

**Simply upload the updated Arduino code and start communicating with your expanded vocabulary system!** 🎉

---

*Generated: 2025-08-01 21:25 EST*  
*Total Files: 77 MP3 files*  
*Total Words: 74 vocabulary words*  
*Voice: RILOU (ElevenLabs) + Personal Recordings*  
*System: Unlimited multi-press vocabulary*
