IsaiahDupree/tactile-comm-device/Audio/VOLUME_UPGRADE_COMPLETE.md

# 🔊 VOLUME UPGRADE COMPLETE!

## 🎯 **ENHANCED VOLUME CONTROL SYSTEM**

Your tactile communication device now has **significantly increased volume** with **precise control options**!

### 📈 **Volume Improvements Made:**

#### **🔊 Higher Default Volume:**
- **Previous**: Volume 10 (moderate)
- **NEW**: Volume 3 (much louder default)
- **Impact**: Device will start up **significantly louder** out of the box

#### **🎛️ Enhanced Volume Controls:**

##### **Quick Controls:**
- **`+`** → **Maximum volume** (1/100) - Nearly full blast!
- **`-`** → **Moderate volume** (15/100) - Comfortable level

##### **Precise Controls (NEW!):**
- **`1`** → **Maximum volume** (1/100) - Loudest possible
- **`2`** → **Very loud** (20/100)
- **`3`** → **Loud** (30/100) 
- **`4`** → **Medium-high** (40/100)
- **`5`** → **Medium** (50/100)
- **`6`** → **Medium-low** (60/100)
- **`7`** → **Low** (70/100)
- **`8`** → **Very low** (80/100)
- **`9`** → **Quiet** (90/100)

#### **📋 Updated Help Menu:**
The device menu now shows: **"+ → Volume up, - → Volume down, 1-9 → Set level"**

### 🎵 **VS1053 Volume Scale:**

**Important**: In VS1053, **lower numbers = louder volume**
- **0** = Maximum possible volume (may cause distortion)
- **1** = Nearly maximum (our new default for `+` and `1`)
- **3** = High volume (our new default startup)
- **10** = Previous default (now much quieter by comparison)
- **100** = Minimum volume (nearly silent)

### 🎮 **How to Use the New Volume System:**

#### **For Maximum Volume:**
1. **Type `1`** in Serial Monitor → Sets to maximum safe volume
2. **Type `+`** → Same as above (quick access)

#### **For Specific Volume Level:**
1. **Type any number 1-9** → Sets precise volume level
2. Device will confirm: `"[AUDIO] Volume set to level X (Y/100)"`

#### **For Quick Adjustments:**
1. **Type `+`** → Quick volume up to maximum
2. **Type `-`** → Quick volume down to moderate level

### 🔧 **Usage Examples:**

```
> 1
[AUDIO] Volume set to level 1 (1/100)    ← Maximum volume

> 5  
[AUDIO] Volume set to level 5 (50/100)   ← Medium volume

> +
[AUDIO] Volume increased to maximum (1/100) ← Quick max

> -
[AUDIO] Volume decreased to moderate (15/100) ← Quick moderate
```

### ✅ **Benefits of the New System:**

#### **🔊 Much Louder Default:**
- Device starts at volume 3 instead of 10
- **Immediately audible** without adjustment
- **Better for communication** needs

#### **🎯 Precise Control:**
- **9 specific volume levels** (1-9)
- **Easy to remember**: 1=loudest, 9=quietest
- **Instant feedback** with confirmation messages

#### **⚡ Quick Access:**
- **`+`** for maximum volume (communication emergencies)
- **`-`** for comfortable volume (normal use)
- **Numbers** for precise adjustment

### 🚀 **Ready to Use:**

Your tactile communication device now has **professional-grade volume control**:

✅ **Starts louder** by default  
✅ **Easy maximum volume** (just press `+` or `1`)  
✅ **Precise level control** (numbers 1-9)  
✅ **Clear feedback** showing current volume  
✅ **Quick adjustments** for any situation  

**Upload the updated Arduino code and enjoy your louder, more controllable communication device!** 🎉

---

*Generated: 2025-08-01 21:29 EST*  
*Default Volume: 3/100 (much louder)*  
*Maximum Volume: 1/100 (nearly full blast)*  
*Control Levels: 9 precise settings*  
*Quick Access: + and - buttons*
