IsaiahDupree/tactile-comm-device/Audio/tactile_communicator_vs1053/LIBRARIES.md

# Required Arduino Libraries

## 📚 Installation Instructions

### Method 1: Arduino IDE Library Manager (Recommended)
1. Open Arduino IDE
2. Go to **Tools → Manage Libraries...**
3. Search for each library below and click **Install**

### Method 2: Manual Installation
Download libraries and place in your Arduino/libraries folder

---

## 🔧 Required Libraries

### 1. Adafruit VS1053 Library ⭐ ESSENTIAL
- **Name**: `Adafruit VS1053 Library`
- **Author**: Adafruit
- **Version**: Latest (1.11.7+)
- **Purpose**: Controls VS1053 codec for high-quality audio playback
- **Dependencies**: Will auto-install SPI library

**Search term**: `Adafruit VS1053`

### 2. Adafruit PCF8575 ⭐ ESSENTIAL  
- **Name**: `Adafruit PCF8575`
- **Author**: Adafruit
- **Version**: Latest (1.1.0+)
- **Purpose**: I2C port expander for 32+ button support
- **Dependencies**: Adafruit_BusIO

**Search term**: `Adafruit PCF8575`

### 3. Standard Libraries (Usually Pre-installed)
These should be included with Arduino IDE:
- **SPI** - Serial Peripheral Interface for VS1053
- **SD** - SD card file operations
- **Wire** - I2C communication for PCF8575

---

## ✅ Installation Verification

### After Installing Libraries:
1. Restart Arduino IDE
2. Go to **Sketch → Include Library**
3. Verify you see:
   - Adafruit VS1053 Library
   - Adafruit PCF8575
   - SD
   - Wire
   - SPI

### Test Compilation:
1. Open `tactile_communicator_vs1053.ino`
2. Select your Arduino board (Tools → Board)
3. Click **Verify** (checkmark icon)
4. Should compile without errors

---

## 🔍 Troubleshooting

### "Library not found" errors:
- Ensure exact library names are installed
- Restart Arduino IDE after installation
- Check Tools → Board selection matches your hardware

### Compilation errors:
- Update Arduino IDE to latest version (1.8.19+ or 2.x)
- Update all libraries to latest versions
- Check board selection (Uno, Nano, etc.)

### Dependency issues:
- Let Arduino IDE auto-install dependencies
- Manually install Adafruit_BusIO if needed

---

## 📦 Alternative: Library Bundle

If you prefer to install all at once, you can create a custom library bundle:

1. Download all required libraries
2. Extract to Arduino/libraries/
3. Restart Arduino IDE
4. Verify all libraries appear in Include Library menu

---

## 🎯 Next Steps
After libraries are installed:
1. Review `WIRING.md` for hardware connections
2. Upload the sketch to your Arduino
3. Open Serial Monitor (9600 baud) for configuration
