IsaiahDupree/tactile-comm-device/Audio/Adafruit_VS1053_Library/player_simple_working_directory_v2/M4_IMPLEMENTATION_STATUS.md

# M4 Update Path Implementation Status

## ✅ COMPLETED FEATURES

### Serial FS Protocol Implementation
- **CRC32 Calculation**: Full lookup table implementation for file integrity verification
- **FSSession Management**: Complete state management for atomic updates
- **Protocol Commands**: All commands implemented:
  - `FS_BEGIN <files> <totalBytes> <manifestCrc32>` - Initialize update session
  - `FS_PUT <path> <size> <crc32>` - Prepare file for transfer
  - `FS_DATA <n>` + binary data - Transfer file chunks
  - `FS_DONE` - Complete current file transfer
  - `FS_COMMIT` - Atomically commit all staged files
  - `FS_ABORT` - Abort update and cleanup staging
  - `CFG_RELOAD` - Reload configuration without reboot
  - `GET_INFO` - Get device information

### Atomic Update Mechanism
- **Staging Directory**: `/_staging` for safe file preparation
- **Rollback Support**: `/_rollback` for recovery from failed updates
- **Maintenance Mode**: Prevents button processing during updates
- **Power-Loss Safety**: Atomic commit ensures consistency

### Integration Points
- **Setup Integration**: FS protocol initialized in `setup()`
- **Main Loop Integration**: FS commands handled with priority
- **Configuration Reload**: Seamless playlist and config refresh
- **Existing System Compatibility**: Works with M1/M2 playlist engine

## 🔧 TECHNICAL ARCHITECTURE

### File Transfer Protocol
```
1. Desktop App → FS_BEGIN (manifest with file count, total size, CRC)
2. For each file:
   a. Desktop App → FS_PUT (path, size, expected CRC)
   b. Desktop App → FS_DATA chunks (512 bytes max per chunk)
   c. Device verifies CRC and responds OK/ERROR
   d. Desktop App → FS_DONE
3. Desktop App → FS_COMMIT (atomically move staging to live)
4. Desktop App → CFG_RELOAD (refresh without reboot)
```

### Safety Features
- **CRC32 Verification**: Every file transfer verified
- **Chunked Transfer**: 512-byte chunks with timeout protection
- **Atomic Operations**: All-or-nothing commit mechanism
- **Error Recovery**: Automatic cleanup on failure
- **Maintenance Mode**: Prevents conflicts during updates

## 📁 SD Card Structure
```
/config/                    # Configuration files
  buttons.csv              # Hardware button mappings (M1)
  mode.cfg                 # Global priority settings (M2)
/mappings/playlists/        # M3U playlist files (M2)
  {KEY}_human.m3u         # Human recordings playlist
  {KEY}_generated.m3u     # Generated audio playlist
/audio/human/{KEY}/         # Human recording audio files
/audio/generated/{KEY}/     # Generated audio files
/state/                     # Runtime state persistence
/_staging/                  # Temporary staging for updates (M4)
/_rollback/                 # Rollback backup directory (M4)
```

## 🎯 M5 DESKTOP APP REQUIREMENTS

### Core Features Needed
1. **Arduino CLI Integration**
   - Auto-detect Arduino boards
   - Flash firmware with progress tracking
   - Stream compilation and upload logs

2. **SD Sync Client**
   - Implement serial FS protocol client
   - Per-file CRC verification and resume
   - Progress tracking and error handling
   - Batch file operations

3. **Self-Test Feature**
   - Play known test audio clip
   - Verify device response
   - Report pass/fail status

4. **One-Click Update Workflow**
   - Flash firmware → SD sync → Self-test
   - Comprehensive error handling
   - User-friendly progress indication

### Desktop App Architecture
```
Desktop App Components:
├── Arduino CLI Wrapper
│   ├── Board detection
│   ├── Firmware compilation
│   └── Upload with logging
├── Serial FS Client
│   ├── Protocol implementation
│   ├── File transfer with resume
│   └── CRC verification
├── Self-Test Module
│   ├── Test audio playback
│   └── Device response validation
└── UI/UX Layer
    ├── Progress indication
    ├── Error reporting
    └── One-click operation
```

## 🚀 NEXT STEPS FOR M5

### Phase 1: Desktop App Foundation
- [ ] Set up Tauri/Electron project structure
- [ ] Integrate Arduino CLI for board detection and flashing
- [ ] Implement serial communication layer
- [ ] Create basic UI for device management

### Phase 2: FS Protocol Client
- [ ] Implement serial FS protocol client
- [ ] Add file transfer with CRC verification
- [ ] Implement resume capability for interrupted transfers
- [ ] Add progress tracking and error handling

### Phase 3: Self-Test Integration
- [ ] Create test audio files and playlists
- [ ] Implement self-test protocol
- [ ] Add device response validation
- [ ] Create comprehensive test reporting

### Phase 4: One-Click Integration
- [ ] Combine flash + sync + test workflow
- [ ] Add comprehensive error handling
- [ ] Implement rollback on failure
- [ ] Create user-friendly progress UI

## 📊 CURRENT STATUS

**M1 (SD Config + Routing)**: ✅ COMPLETE
- Hardware-agnostic button mapping via CSV
- PCF and GPIO input support
- Dynamic memory allocation

**M2 (Playlist Engine)**: ✅ COMPLETE  
- M3U playlist parsing and caching
- Priority mode integration
- Multi-press support with cursor management

**M4 (Update Path)**: ✅ COMPLETE
- Serial FS protocol fully implemented
- Atomic update mechanism ready
- Desktop app integration points prepared

**M5 (Desktop App)**: 🔄 READY TO START
- All backend protocols implemented
- Clear requirements and architecture defined
- Ready for desktop application development

## 🔍 TESTING RECOMMENDATIONS

### M4 Protocol Testing
1. **Basic Transfer Test**: Single file upload via serial
2. **Multi-File Test**: Complete playlist update
3. **Error Recovery Test**: Interrupted transfer handling
4. **Power-Loss Test**: Staging directory integrity
5. **CRC Verification Test**: Corrupted file detection

### M5 Integration Testing  
1. **End-to-End Test**: Flash → Sync → Test workflow
2. **Error Handling Test**: Various failure scenarios
3. **Resume Test**: Interrupted transfer recovery
4. **Performance Test**: Large file transfer speeds
5. **User Experience Test**: One-click operation flow

---

**CONCLUSION**: M4 milestone is functionally complete with a robust, atomic SD card update protocol. The system is ready for M5 desktop application development, which will provide the user-friendly interface for device management and updates.
