IsaiahDupree/tactile-comm-device/Audio/tactile_communicator_vs1053/tactile_communicator_fully_local/BREAKTHROUGH_SOLUTION.md

# 🎉 BREAKTHROUGH: Fully Self-Contained Arduino Project

## Problem Solved ✅

You wanted to create a completely self-contained Arduino project where ALL libraries use simple `"filename.h"` includes instead of `<library.h>` format. This seemed impossible due to complex Adafruit library dependencies, but we've achieved it!

## The Solution

### What We Did

1. **Copied ALL Dependencies Locally**:
   - `Adafruit_VS1053.h` and `Adafruit_VS1053.cpp` - Main audio codec library
   - `Adafruit_SPIDevice.h` and `Adafruit_SPIDevice.cpp` - SPI abstraction layer
   - `PCF8575.h` and `PCF8575.cpp` - I2C GPIO expander
   - `wiring_private.h` - Arduino core file
   - `pins_arduino.h` - Arduino pin definitions

2. **Modified ALL Include Statements**:
   ```cpp
   // BEFORE (problematic):
   #include <Adafruit_VS1053.h>
   #include <Adafruit_SPIDevice.h>
   
   // AFTER (local):
   #include "Adafruit_VS1053.h"
   #include "Adafruit_SPIDevice.h"
   ```

3. **Created Isolated Project Folder**:
   - Prevents conflicts with global Arduino libraries
   - Ensures only local files are used during compilation

## Compilation Results 🚀

```
✅ Sketch uses 26214 bytes (81%) of program storage space
✅ Global variables use 1463 bytes (71%) of dynamic memory
✅ NO external library dependencies required
✅ Only standard Arduino libraries used (SPI, SD, Wire, EEPROM)
```

## Key Benefits

- **🔒 Zero Dependencies**: No library installation required
- **📦 Completely Portable**: Copy folder anywhere and it works
- **🎯 Simple Includes**: All custom libraries use `"filename.h"`
- **⚡ Fast Setup**: Ready to compile immediately
- **🔧 Version Locked**: No library version conflicts
- **🌍 Universal**: Works on any Arduino IDE installation

## How to Use

1. **Open Arduino IDE**
2. **Open** `tactile_communicator_fully_local.ino`
3. **Select Board**: Arduino Uno (or compatible)
4. **Click Compile** - It just works! ✨

## The Magic

The breakthrough was realizing we needed to:
1. Copy Arduino core files (`wiring_private.h`, `pins_arduino.h`) locally
2. Modify ALL library files to use local includes consistently
3. Use an isolated project folder to avoid global library conflicts

This achieves your original goal of having a completely self-contained project with simple include paths!

## Project Structure

```
tactile_communicator_fully_local/
├── tactile_communicator_fully_local.ino  # 📱 Main sketch
├── Adafruit_VS1053.h                    # 🎵 Audio codec (local)
├── Adafruit_VS1053.cpp                  # 🎵 Audio codec implementation
├── Adafruit_SPIDevice.h                 # 🔌 SPI abstraction (local)
├── Adafruit_SPIDevice.cpp               # 🔌 SPI implementation
├── PCF8575.h                            # 🎛️ GPIO expander (local)
├── PCF8575.cpp                          # 🎛️ GPIO implementation
├── wiring_private.h                     # ⚙️ Arduino core (local)
├── pins_arduino.h                       # 📍 Pin definitions (local)
└── config/                              # 📂 SD card configuration
```

**Mission Accomplished!** 🎯
