IsaiahDupree/tactile-comm-device/Audio/tactile_communicator_vs1053/tactile_communicator_fully_local/LIBRARY_INFO.md

# Library Compatibility Information

## Local Libraries Included

### 1. Adafruit_VS1053_Library
- **Source**: Official Adafruit library
- **Version**: Latest from your Arduino libraries folder
- **Purpose**: VS1053 audio codec control
- **Files**: `Adafruit_VS1053.h`, `Adafruit_VS1053.cpp`
- **Status**: ✅ Compatible - No changes needed

### 2. PCF8575
- **Source**: RobTillaart/PCF8575 (GitHub)
- **Version**: 0.2.4
- **Purpose**: I2C GPIO expander (16-bit)
- **Files**: `PCF8575.h`, `PCF8575.cpp`
- **Status**: ✅ Compatible - Code updated to use `read16()` method

## Code Modifications Made

### Include Path Updates
Updated include statements to use simple double-quoted format (library files are at the same level as .ino file):

```cpp
// Standard Arduino libraries (angle brackets):
#include <SPI.h>
#include <SD.h>
#include <Wire.h>
#include <EEPROM.h>

// Local libraries (double quotes, same folder level):
#include "Adafruit_VS1053.h"
#include "PCF8575.h"
```

### PCF8575 Method Updates
The original code used `digitalReadWord()` which doesn't exist in the RobTillaart library.
Updated to use the correct method:

```cpp
// OLD (incompatible):
uint16_t s0 = pcf0.digitalReadWord();

// NEW (compatible):
uint16_t s0 = pcf0.read16();
```

### Library API Mapping
| Original Method | RobTillaart Method | Purpose |
|---|---|---|
| `digitalReadWord()` | `read16()` | Read all 16 pins as uint16_t |
| `begin()` | `begin()` | Initialize PCF8575 |

## Standard Arduino Libraries
These are built-in and require no local copies:
- `SPI.h` - Serial Peripheral Interface
- `SD.h` - SD card support
- `Wire.h` - I2C communication
- `EEPROM.h` - EEPROM memory access

## Verification Steps

1. **Library Structure Check**:
   ```
   tactile_communicator_local_libs/
   ├── tactile_communicator_local_libs.ino
   ├── Adafruit_VS1053.h
   ├── Adafruit_VS1053.cpp
   ├── PCF8575.h
   ├── PCF8575.cpp
   └── config/
   ```

2. **Compilation Test**:
   - Open `tactile_communicator_local_libs.ino` in Arduino IDE
   - Arduino IDE automatically detects local libraries
   - Verify compilation with your target board selected

3. **Runtime Test**:
   - Upload to Arduino with proper hardware connections
   - Check serial monitor for initialization messages
   - Test button mappings and audio playback

## Troubleshooting

### Compilation Errors
- **"PCF8575.h not found"**: Verify library folder structure
- **"digitalReadWord not declared"**: Code should be updated (already done)
- **VS1053 errors**: Check Adafruit library version compatibility

### Runtime Issues
- **I2C errors**: Check PCF8575 wiring and addresses (0x20, 0x21)
- **SD card errors**: Verify SD card format (FAT32) and wiring
- **Audio issues**: Check VS1053 connections and MP3 file formats

## Hardware Requirements

- Arduino Uno/Nano/Mega (or compatible)
- VS1053 Audio Codec Breakout
- 1-2 PCF8575 I2C GPIO Expanders
- SD Card (FAT32 formatted)
- Tactile buttons
- Audio output device

This project is now fully self-contained with all required libraries included locally.
