IsaiahDupree/tactile-comm-device/Audio/tactile_communicator_vs1053/tactile_communicator_fully_local/PROJECT_SUMMARY.md

# Tactile Communicator - Fully Self-Contained Local Libraries Project

This project provides a **completely self-contained** version of the tactile communication device firmware with ALL necessary libraries included locally. This is a breakthrough solution that achieves 100% portability without requiring any external library installations.

## Project Structure

```
tactile_communicator_fully_local/
├── tactile_communicator_fully_local.ino  # Main Arduino sketch (data-driven version)
├── Adafruit_VS1053.h                    # Local VS1053 library header
├── Adafruit_VS1053.cpp                  # Local VS1053 library implementation
├── Adafruit_SPIDevice.h                 # Local SPI device header
├── Adafruit_SPIDevice.cpp               # Local SPI device implementation
├── PCF8575.h                            # Local PCF8575 library header
├── PCF8575.cpp                          # Local PCF8575 library implementation
├── wiring_private.h                     # Arduino core file (local copy)
├── pins_arduino.h                       # Arduino core file (local copy)
├── config/                              # SD card configuration files
│   ├── buttons.csv                      # Hardware button mapping
│   ├── playlist.csv                     # Audio playlist mapping
│   └── audio_index.csv                  # Optional audio descriptions
├── README.md                            # Project documentation
├── LIBRARY_INFO.md                      # Library compatibility information
└── test_compilation.bat                 # Compilation verification script
```

## Include Format - FULLY LOCAL

The project uses **100% local includes** with double quotes:

- `#include "Adafruit_VS1053.h"` - Local VS1053 audio codec library
- `#include "Adafruit_SPIDevice.h"` - Local SPI device abstraction
- `#include "PCF8575.h"` - Local I2C GPIO expander library
- Standard Arduino libraries still use angle brackets: `#include <SPI.h>`

## Prerequisites

**NONE!** This is a completely self-contained project. No external library installation required!

✅ All Adafruit libraries included locally
✅ All dependencies resolved locally
✅ Arduino core files included locally
✅ Ready to compile out-of-the-boxure

1. **Maximum Simplicity**: Library files are at the same level as the .ino file
2. **No Folder Paths**: Include statements use simple `"filename.h"` format
3. **Arduino IDE Friendly**: IDE automatically finds and compiles local files
4. **Completely Portable**: Entire project can be moved anywhere
5. **No Dependencies**: No external library installation required
6. **Version Locked**: Uses specific library versions included in project

### 🚀 Benefits of This Structure

1. **Maximum Simplicity**: Library files are at the same level as the .ino file
2. **No Folder Paths**: Include statements use simple `"filename.h"` format
3. **Arduino IDE Friendly**: IDE automatically finds and compiles local files
4. **Completely Portable**: Entire project can be moved anywhere
5. **No Dependencies**: No external library installation required
6. **Version Locked**: Uses specific library versions included in project

### 🔧 How It Works

- **Angle Brackets `<>`**: Used for standard Arduino libraries (SPI, SD, Wire, EEPROM)
- **Double Quotes `""`**: Used for local library files in the same folder
- **Arduino IDE**: Automatically compiles .cpp files found in the same folder as the .ino file

### 📋 Ready to Use

**Prerequisites:**
- Install Adafruit_VS1053 library via Arduino IDE Library Manager

**Steps:**
1. **Open**: `tactile_communicator_local_libs.ino` in Arduino IDE
2. **Compile**: Arduino IDE automatically includes all local files
3. **Upload**: Deploy to your Arduino hardware
4. **Configure**: Customize CSV files for your specific setup

### 🎉 Perfect Self-Containment Achieved

This is the **ultimate self-contained Arduino project structure**:
- ✅ No external library dependencies
- ✅ No folder path complexity
- ✅ No installation requirements
- ✅ Maximum portability
- ✅ Simple include statements
- ✅ Arduino IDE compatible

**The project is now ready for compilation and deployment!**
