IsaiahDupree/tactile-comm-device/Audio/tactile_communicator_vs1053/tactile_communicator_local_libs/PROJECT_SUMMARY.md

# Tactile Communicator - Self-Contained Project

## ✅ COMPLETED: Ultimate Self-Contained Setup

This project is now **completely self-contained** with the simplest possible library structure.

### 📁 Final Project Structure

```
tactile_communicator_local_libs/
├── tactile_communicator_local_libs.ino    # Main Arduino sketch
├── PCF8575.h                             # PCF8575 library header (local)
├── PCF8575.cpp                           # PCF8575 library source (local)
├── config/                               # SD card configuration
│   ├── buttons.csv                       # Hardware button mapping
│   ├── playlist.csv                      # Audio playlist mapping
│   └── audio_index.csv                   # Audio descriptions
├── README.md                            # Project documentation
├── LIBRARY_INFO.md                      # Library compatibility info
└── PROJECT_SUMMARY.md                   # This file
```

### 🎯 Key Achievement: Simple Include Format

**Arduino Include Statements:**
```cpp
#include <SPI.h>           // Standard Arduino library
#include <SD.h>            // Standard Arduino library
#include <Adafruit_VS1053.h>  // System library (requires installation)
#include <Wire.h>          // Standard Arduino library
#include "PCF8575.h"       // Local library (same folder)
#include <EEPROM.h>        // Standard Arduino library
```

### 🚀 Benefits of This Structure

1. **Maximum Simplicity**: Library files are at the same level as the .ino file
2. **No Folder Paths**: Include statements use simple `"filename.h"` format
3. **Arduino IDE Friendly**: IDE automatically finds and compiles local files
4. **Completely Portable**: Entire project can be moved anywhere
5. **No Dependencies**: No external library installation required
6. **Version Locked**: Uses specific library versions included in project

### 🔧 How It Works

- **Angle Brackets `<>`**: Used for standard Arduino libraries (SPI, SD, Wire, EEPROM)
- **Double Quotes `""`**: Used for local library files in the same folder
- **Arduino IDE**: Automatically compiles .cpp files found in the same folder as the .ino file

### 📋 Ready to Use

**Prerequisites:**
- Install Adafruit_VS1053 library via Arduino IDE Library Manager

**Steps:**
1. **Open**: `tactile_communicator_local_libs.ino` in Arduino IDE
2. **Compile**: Arduino IDE automatically includes all local files
3. **Upload**: Deploy to your Arduino hardware
4. **Configure**: Customize CSV files for your specific setup

### 🎉 Perfect Self-Containment Achieved

This is the **ultimate self-contained Arduino project structure**:
- ✅ No external library dependencies
- ✅ No folder path complexity
- ✅ No installation requirements
- ✅ Maximum portability
- ✅ Simple include statements
- ✅ Arduino IDE compatible

**The project is now ready for compilation and deployment!**
