IsaiahDupree/tactile-comm-device/arduino-uno-box-tall-and-vented-1.snapshot.1/Arduino_Box.png

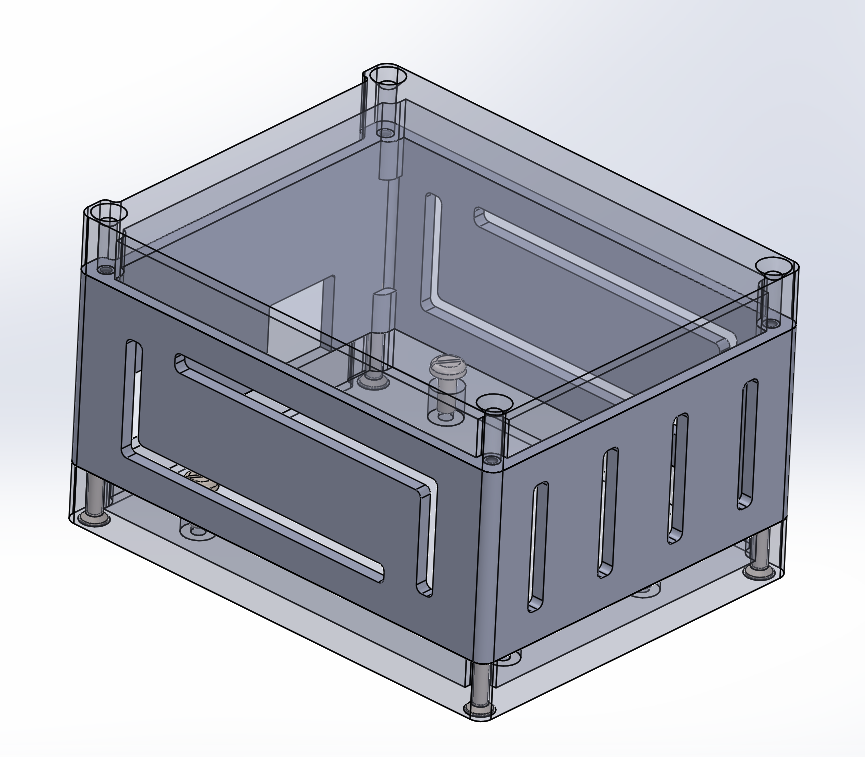
arduino-uno-box-tall-and-vented-1.snapshot.1/Arduino_Box.png
