IsaiahDupree/tactile-comm-device/arduino-uno-case-8.snapshot.1/ArduinoUno case/IMG-20210529-WA0004.jpg

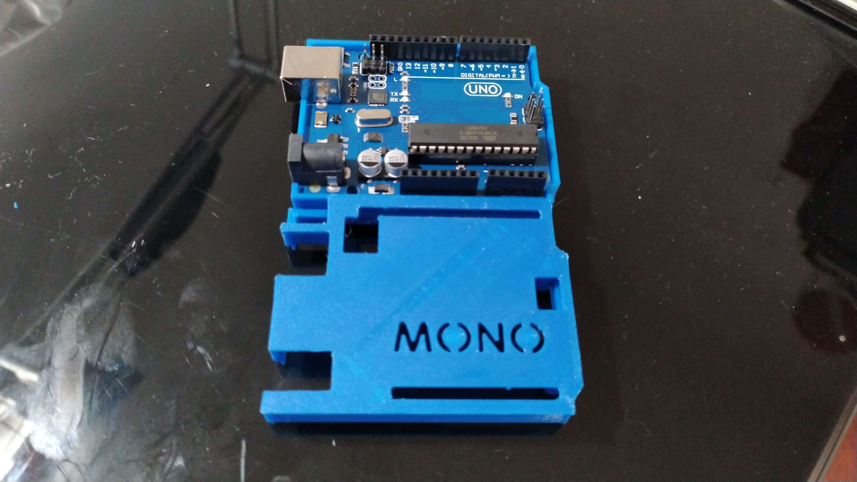
arduino-uno-case-8.snapshot.1/ArduinoUno case/IMG-20210529-WA0004.jpg
