IsaiahDupree/tactile-comm-device/mini-speaker-4ohm-3watt-1.snapshot.2/minispeaker.png

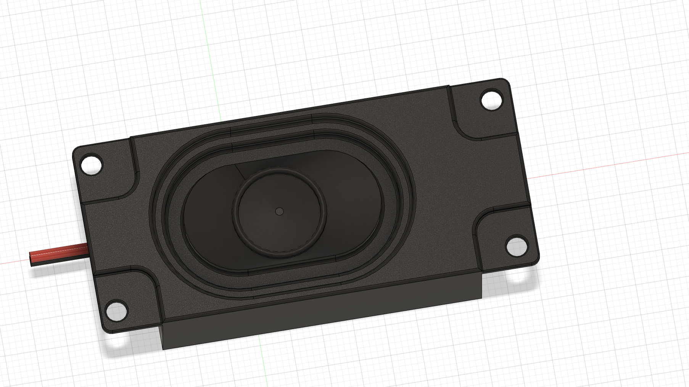
mini-speaker-4ohm-3watt-1.snapshot.2/minispeaker.png
