IsaiahDupree/tactile-comm-device/momentary-push-button-switch-4.snapshot.3/generic-momentary-switch-2.jpg

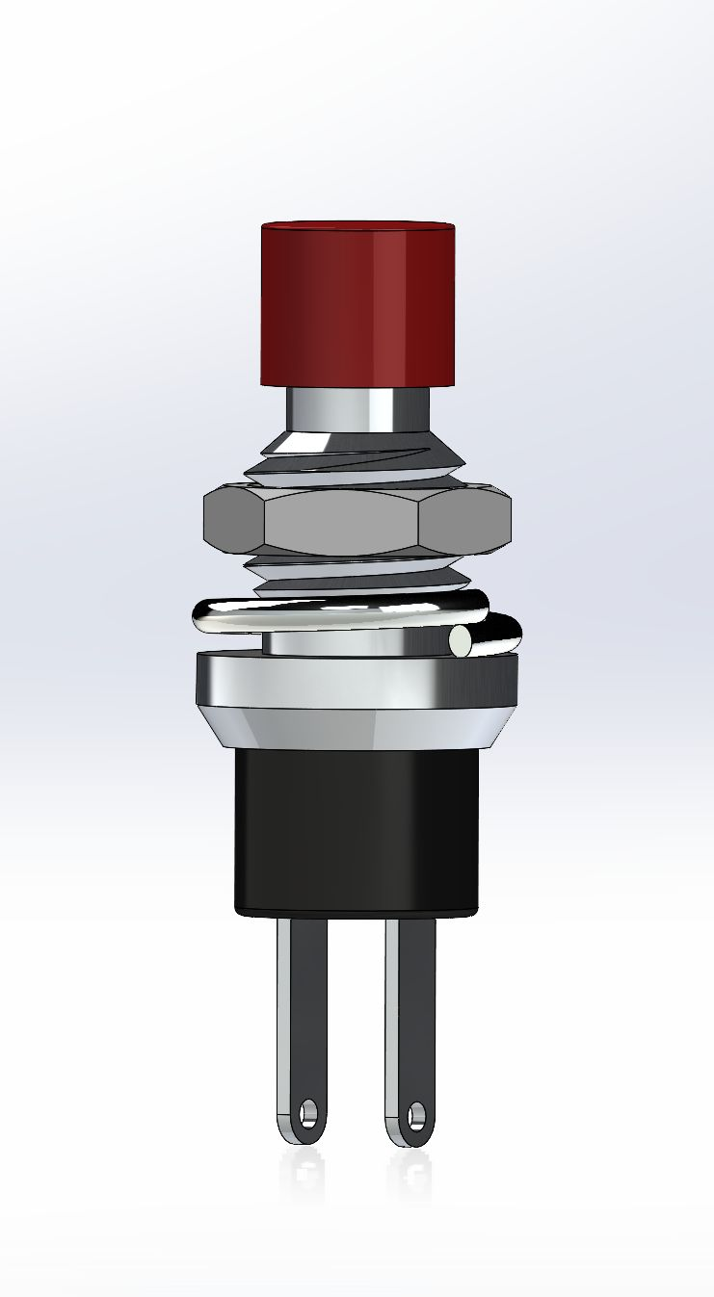
momentary-push-button-switch-4.snapshot.3/generic-momentary-switch-2.jpg
