IsaiahDupree/tactile-comm-device/type-a_usb-male-1.snapshot.1/1.png

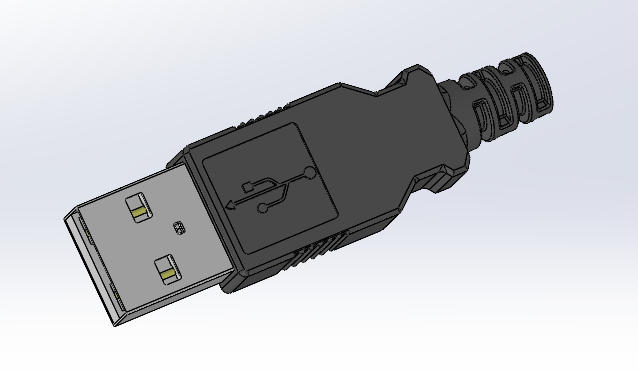
type-a_usb-male-1.snapshot.1/1.png
