IsaiahDupree/tactile-comm-device/momentary-push-button-switch-4.snapshot.3/momentary-pushbutton-switch-body.SLDPRT

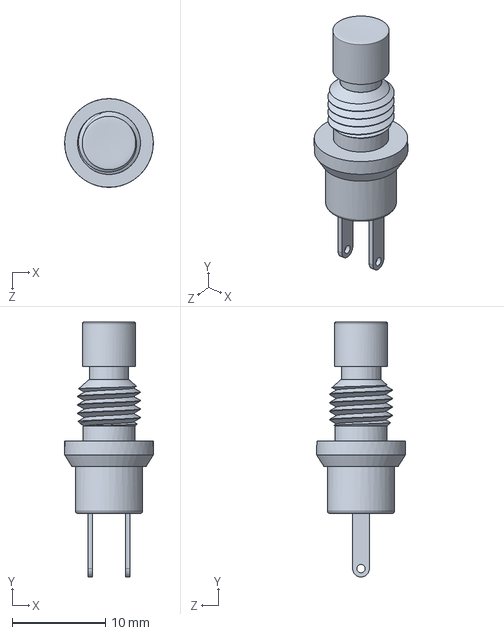
[picture p22: CAD file, 2025-08-17]
momentary-push-button-switch-4.snapshot.3/momentary-pushbutton-switch-body.SLDPRT
9.49 x 27.3 x 9.50 mm
