IsaiahDupree/tactile-comm-device/arduino-uno-box-tall-and-vented-1.snapshot.1/Box_arduino.STEP

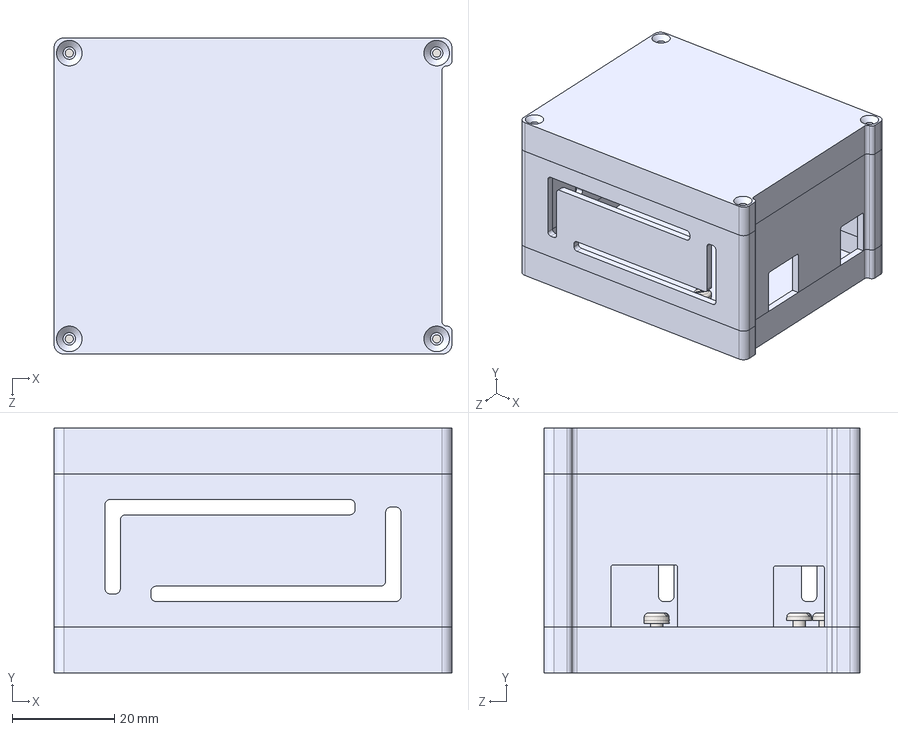
[picture p23: CAD file, 2025-08-17]
arduino-uno-box-tall-and-vented-1.snapshot.1/Box_arduino.STEP
78.0 x 48.0 x 62.0 mm
Box_arduino_base
Box_arduino_side
Box_arduino_cover
flat head screw_am_B18.6.7M - M2 x 0.4 x 16 Type I Cross Recessed FHMS --16N x 5
slotted pan head screw_iso_ISO 1580 - M2.5 x 6 - 6N x 5
