IsaiahDupree/tactile-comm-device/momentary-push-button-switch-4.snapshot.3/momentary-pushbutton-switch.STEP

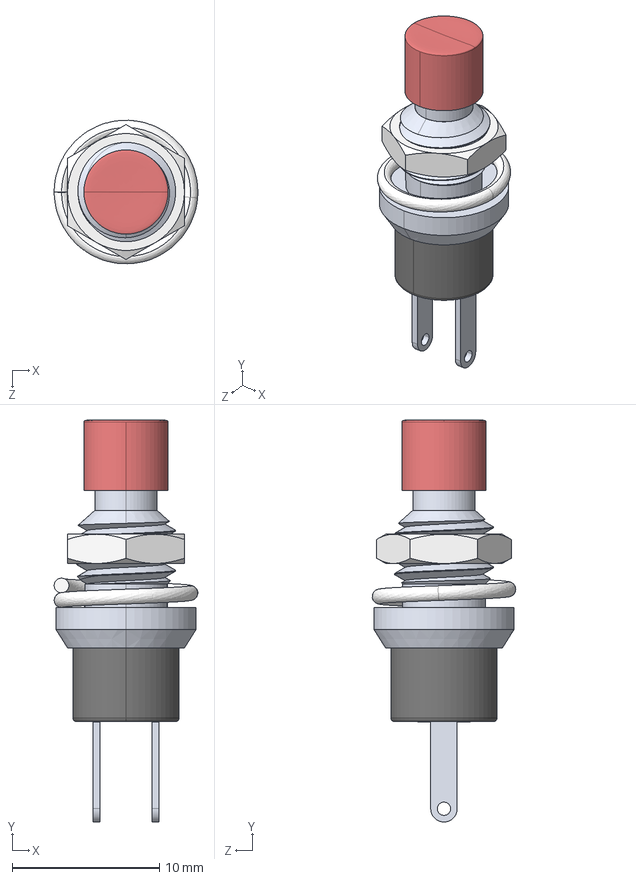
[picture p24: CAD file, 2025-08-17]
momentary-push-button-switch-4.snapshot.3/momentary-pushbutton-switch.STEP
9.76 x 27.3 x 9.75 mm
momentary-pushbutton-switch-body
split-wire-ring
91862A311_HEX PANEL NUT_91862A311
