IsaiahDupree/tactile-comm-device/arduino-uno-box-tall-and-vented-1.snapshot.1/Box_arduino_base.SLDPRT

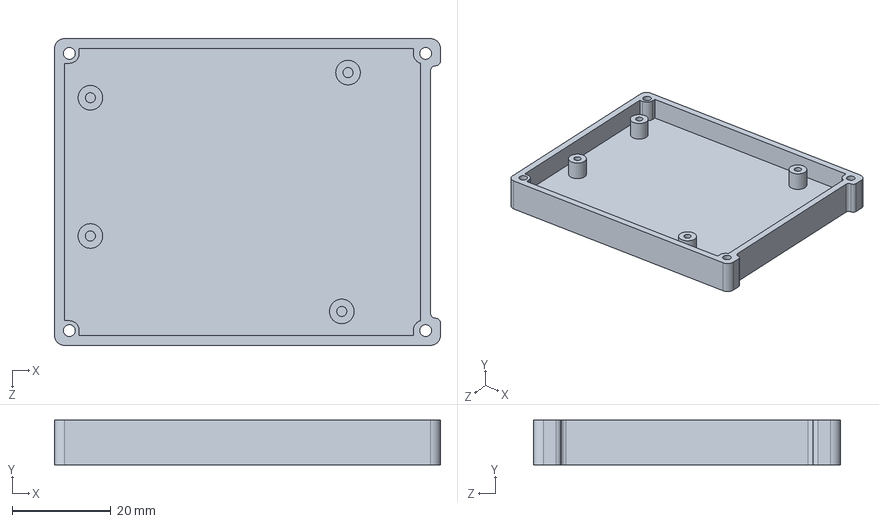
[picture p25: CAD file, 2025-08-17]
arduino-uno-box-tall-and-vented-1.snapshot.1/Box_arduino_base.SLDPRT
78.0 x 9.00 x 62.0 mm
