IsaiahDupree/tactile-comm-device/arduino-uno-case-8.snapshot.1/ArduinoUno case/CE3_Auno carcasa abajo.3mf

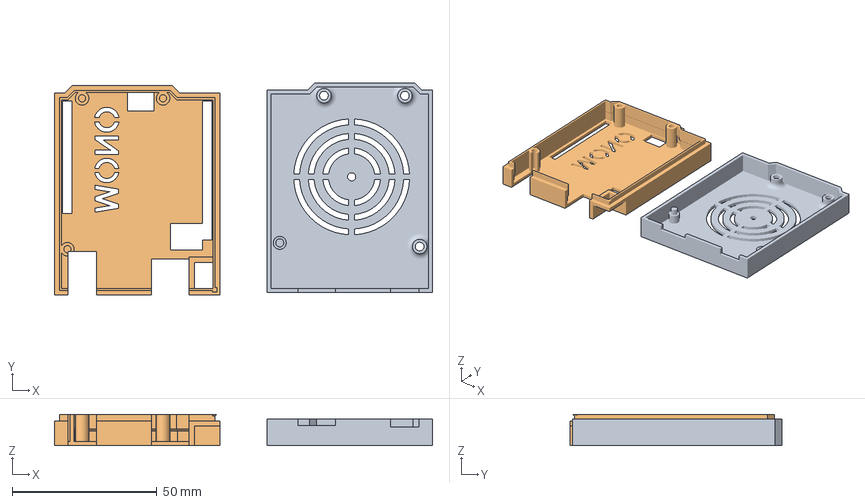
[picture p26: CAD file, 2025-08-17]
arduino-uno-case-8.snapshot.1/ArduinoUno case/CE3_Auno carcasa abajo.3mf
130.4 x 73.3 x 10.7 mm
Auno carcasa abajo.STL
Auno carcasa arriba.STL
