IsaiahDupree/tactile-comm-device/momentary-push-button-switch-4.snapshot.3/split-wire-ring.SLDPRT

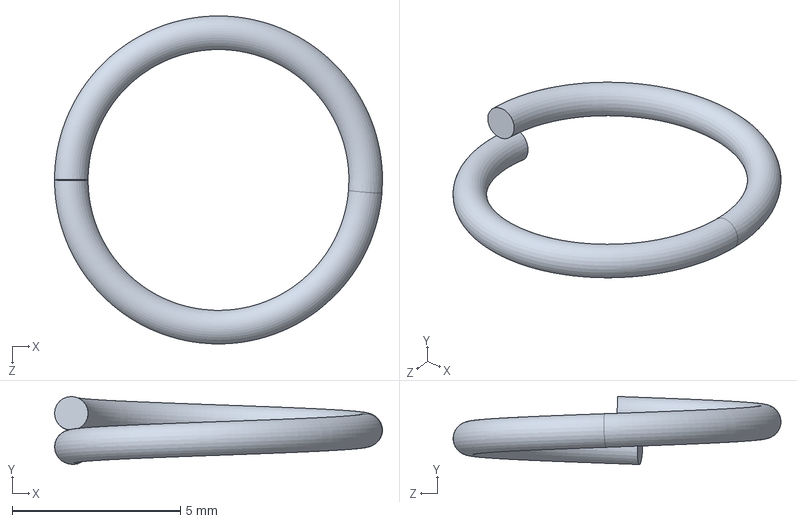
[picture p27: CAD file, 2025-08-17]
momentary-push-button-switch-4.snapshot.3/split-wire-ring.SLDPRT
9.76 x 2.02 x 9.76 mm
