IsaiahDupree/tactile-comm-device/arduino-uno-box-tall-and-vented-1.snapshot.1/Box_arduino_cover.SLDPRT

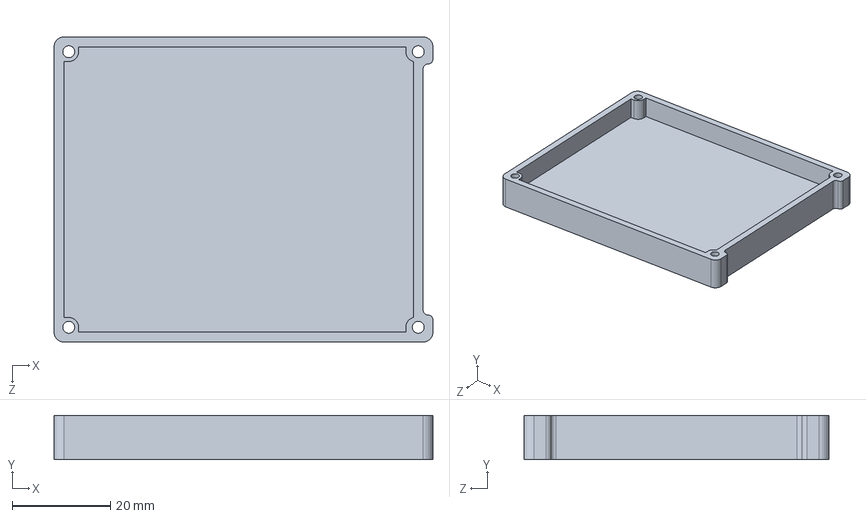
[picture p28: CAD file, 2025-08-17]
arduino-uno-box-tall-and-vented-1.snapshot.1/Box_arduino_cover.SLDPRT
77.0 x 9.00 x 62.0 mm
