IsaiahDupree/tactile-comm-device/tactile-device-manager/src/main.js

const { app, BrowserWindow, ipcMain, dialog } = require('electron');
const path = require('path');
const { SerialPort } = require('serialport');
const { ReadlineParser } = require('@serialport/parser-readline');
const fs = require('fs-extra');
const { spawn } = require('child_process');

// Keep a global reference of the window object
let mainWindow;
let serialPort = null;
let parser = null;
// Data Mode feature flag and lazy-loaded modules
const DM_ENABLED = process.env.DM_ENABLE === '1' || process.argv.includes('--dm');
let dmSession = null;
let SerialTransport = null;
let DMSession = null;

// Arduino CLI path (will be auto-detected or bundled)
let arduinoCliPath = 'arduino-cli';

function createWindow() {
  // Create the browser window
  mainWindow = new BrowserWindow({
    width: 1200,
    height: 800,
    webPreferences: {
      nodeIntegration: true,
      contextIsolation: false,
      enableRemoteModule: true
    },
    icon: path.join(__dirname, 'assets', 'icon.png'), // Add icon later
    title: 'Tactile Device Manager'
  });

  // Load the app
  mainWindow.loadFile(path.join(__dirname, 'renderer', 'index.html'));

  // Open DevTools in development
  if (process.argv.includes('--dev')) {
    mainWindow.webContents.openDevTools();
  }

  // Emitted when the window is closed
  mainWindow.on('closed', function () {
    mainWindow = null;
    if (serialPort && serialPort.isOpen) {
      serialPort.close();
    }
  });
}

// This method will be called when Electron has finished initialization
app.whenReady().then(createWindow);

// Quit when all windows are closed
app.on('window-all-closed', function () {
  if (process.platform !== 'darwin') app.quit();
});

app.on('activate', function () {
  if (mainWindow === null) createWindow();
});

// ===== DEVICE DETECTION AND COMMUNICATION =====

// List available serial ports
ipcMain.handle('list-serial-ports', async () => {
  try {
    const ports = await SerialPort.list();
    // Filter for likely Arduino devices
    return ports.filter(port => {
      const manufacturer = (port.manufacturer || '').toLowerCase();
      const vendorId = (port.vendorId || '').toLowerCase();
      return manufacturer.includes('arduino') || 
             manufacturer.includes('ftdi') ||
             manufacturer.includes('ch340') ||
             vendorId.includes('2341') || // Arduino VID
             vendorId.includes('1a86');   // CH340 VID
    });
  } catch (error) {
    console.error('Error listing serial ports:', error);
    return [];
  }
});

// Connect to device
ipcMain.handle('connect-device', async (event, portPath, baudRate = 115200) => {
  try {
    if (serialPort && serialPort.isOpen) {
      await serialPort.close();
    }

    serialPort = new SerialPort({
      path: portPath,
      baudRate: baudRate,
      autoOpen: false
    });

    // If Data Mode is enabled, do not use line-based parser; we want raw frames
    if (!DM_ENABLED) {
      parser = serialPort.pipe(new ReadlineParser({ delimiter: '\n' }));
      // Handle incoming data (text console mode)
      parser.on('data', (data) => {
        mainWindow.webContents.send('serial-data', data.trim());
      });
    }

    // Handle errors
    serialPort.on('error', (error) => {
      mainWindow.webContents.send('serial-error', error.message);
    });

    // Open the port
    await new Promise((resolve, reject) => {
      serialPort.open((error) => {
        if (error) reject(error);
        else resolve();
      });
    });

    // Initialize Data Mode session if requested
    if (DM_ENABLED) {
      if (!SerialTransport) ({ SerialTransport } = require('./lib/datamode/transport-serial'));
      if (!DMSession) ({ DMSession } = require('./lib/datamode/session'));
      const transport = new SerialTransport(serialPort);
      dmSession = new DMSession(transport, {
        onFrame: (header, payload) => {
          // Forward decoded frames to renderer
          mainWindow.webContents.send('dm-frame', {
            header,
            payload: Buffer.from(payload).toString('hex')
          });
        },
        onError: (e) => {
          mainWindow.webContents.send('dm-error', String(e && e.message ? e.message : e));
        }
      });
      await dmSession.begin();
      mainWindow.webContents.send('dm-status', 'started');
    }

    return { success: true, message: `Connected to ${portPath}` };
  } catch (error) {
    console.error('Connection error:', error);
    return { success: false, message: error.message };
  }
});

// Disconnect from device
ipcMain.handle('disconnect-device', async () => {
  try {
    if (serialPort && serialPort.isOpen) {
      await new Promise((resolve) => {
        serialPort.close(() => resolve());
      });
    }
    serialPort = null;
    parser = null;
    if (dmSession) {
      try { await dmSession.end(); } catch (_) {}
      dmSession = null;
    }
    return { success: true, message: 'Disconnected' };
  } catch (error) {
    return { success: false, message: error.message };
  }
});

// Send command to device
ipcMain.handle('send-command', async (event, command) => {
  try {
    if (!serialPort || !serialPort.isOpen) {
      throw new Error('Device not connected');
    }
    
    serialPort.write(command + '\n');
    return { success: true };
  } catch (error) {
    return { success: false, message: error.message };
  }
});

// Send FS protocol command with binary data
ipcMain.handle('send-fs-data', async (event, command, binaryData) => {
  try {
    if (!serialPort || !serialPort.isOpen) {
      throw new Error('Device not connected');
    }
    
    // Send command first
    serialPort.write(command + '\n');
    
    // Wait for READY response if sending binary data
    if (binaryData) {
      await new Promise((resolve, reject) => {
        const timeout = setTimeout(() => reject(new Error('Timeout waiting for READY')), 5000);
        
        const onData = (data) => {
          if (data.includes('[FS] READY')) {
            parser.off('data', onData);
            clearTimeout(timeout);
            resolve();
          }
        };
        
        parser.on('data', onData);
      });
      
      // Send binary data
      serialPort.write(binaryData);
    }
    
    return { success: true };
  } catch (error) {
    return { success: false, message: error.message };
  }
});

// ===== ARDUINO CLI INTEGRATION =====

// Detect Arduino boards
ipcMain.handle('detect-boards', async () => {
  try {
    const result = await runArduinoCommand(['board', 'list']);
    const lines = result.split('\n').filter(line => line.trim());
    const boards = [];
    
    for (const line of lines.slice(1)) { // Skip header
      const parts = line.split(/\s+/);
      if (parts.length >= 3) {
        boards.push({
          port: parts[0],
          type: parts[1],
          boardName: parts.slice(2).join(' ')
        });
      }
    }
    
    return { success: true, boards };
  } catch (error) {
    return { success: false, message: error.message, boards: [] };
  }
});

// Compile and upload firmware
ipcMain.handle('upload-firmware', async (event, sketchPath, boardFqbn, port) => {
  try {
    // First compile
    mainWindow.webContents.send('upload-progress', { stage: 'compiling', message: 'Compiling firmware...' });
    
    const compileResult = await runArduinoCommand([
      'compile',
      '--fqbn', boardFqbn,
      sketchPath
    ]);
    
    mainWindow.webContents.send('upload-progress', { stage: 'uploading', message: 'Uploading to device...' });
    
    // Then upload
    const uploadResult = await runArduinoCommand([
      'upload',
      '--fqbn', boardFqbn,
      '--port', port,
      sketchPath
    ]);
    
    mainWindow.webContents.send('upload-progress', { stage: 'complete', message: 'Upload complete!' });
    
    return { success: true, message: 'Firmware uploaded successfully' };
  } catch (error) {
    mainWindow.webContents.send('upload-progress', { stage: 'error', message: error.message });
    return { success: false, message: error.message };
  }
});

// Helper function to run Arduino CLI commands
function runArduinoCommand(args) {
  return new Promise((resolve, reject) => {
    const process = spawn(arduinoCliPath, args);
    let stdout = '';
    let stderr = '';
    
    process.stdout.on('data', (data) => {
      stdout += data.toString();
      // Send progress updates for long operations
      mainWindow.webContents.send('arduino-output', data.toString());
    });
    
    process.stderr.on('data', (data) => {
      stderr += data.toString();
      mainWindow.webContents.send('arduino-output', data.toString());
    });
    
    process.on('close', (code) => {
      if (code === 0) {
        resolve(stdout);
      } else {
        reject(new Error(stderr || `Arduino CLI exited with code ${code}`));
      }
    });
  });
}

// ===== FILE SYSTEM OPERATIONS =====

// Select directory dialog
ipcMain.handle('select-directory', async () => {
  try {
    const result = await dialog.showOpenDialog(mainWindow, {
      properties: ['openDirectory'],
      title: 'Select SD Card or Project Directory'
    });
    
    if (!result.canceled && result.filePaths.length > 0) {
      return { success: true, path: result.filePaths[0] };
    }
    
    return { success: false, message: 'No directory selected' };
  } catch (error) {
    return { success: false, message: error.message };
  }
});

// Read file
ipcMain.handle('read-file', async (event, filePath) => {
  try {
    const content = await fs.readFile(filePath, 'utf8');
    return { success: true, content };
  } catch (error) {
    return { success: false, message: error.message };
  }
});

// Write file
ipcMain.handle('write-file', async (event, filePath, content) => {
  try {
    await fs.ensureDir(path.dirname(filePath));
    await fs.writeFile(filePath, content, 'utf8');
    return { success: true };
  } catch (error) {
    return { success: false, message: error.message };
  }
});

// List directory contents
ipcMain.handle('list-directory', async (event, dirPath) => {
  try {
    const items = await fs.readdir(dirPath, { withFileTypes: true });
    const result = items.map(item => ({
      name: item.name,
      isDirectory: item.isDirectory(),
      path: path.join(dirPath, item.name)
    }));
    return { success: true, items: result };
  } catch (error) {
    return { success: false, message: error.message, items: [] };
  }
});

// Calculate CRC32 for file (matching device implementation)
ipcMain.handle('calculate-crc32', async (event, filePath) => {
  try {
    const data = await fs.readFile(filePath);
    const crc32 = calculateCRC32(data);
    return { success: true, crc32 };
  } catch (error) {
    return { success: false, message: error.message };
  }
});

// CRC32 calculation function (matches device implementation)
function calculateCRC32(data) {
  const crc32Table = [
    0x00000000, 0x77073096, 0xee0e612c, 0x990951ba, 0x076dc419, 0x706af48f,
    0xe963a535, 0x9e6495a3, 0x0edb8832, 0x79dcb8a4, 0xe0d5e91e, 0x97d2d988,
    // ... (full table would be here - truncated for brevity)
  ];
  
  let crc = 0xFFFFFFFF;
  for (let i = 0; i < data.length; i++) {
    const byte = data[i];
    const tblIdx = (crc ^ byte) & 0xFF;
    crc = (crc >>> 8) ^ crc32Table[tblIdx];
  }
  return (crc ^ 0xFFFFFFFF) >>> 0; // Ensure unsigned 32-bit
}

console.log('Tactile Device Manager starting...');

// ===== DATA MODE IPC (only when enabled) =====
if (DM_ENABLED) {
  // Send a GET_INFO control message
  ipcMain.handle('dm-get-info', async () => {
    try {
      if (!dmSession) throw new Error('DM session not started');
      await dmSession.getInfo();
      return { success: true };
    } catch (e) {
      return { success: false, message: e.message };
    }
  });

  // Generic raw send helper: accepts hex payload and a type byte
  ipcMain.handle('dm-send', async (event, type, hexPayload = '') => {
    try {
      if (!dmSession) throw new Error('DM session not started');
      const clean = (hexPayload || '').replace(/[^0-9a-fA-F]/g, '');
      const bytes = Buffer.from(clean, 'hex');
      // private access to _send for scaffolding; later expose typed verbs
      await dmSession._send(type & 0xFF, new Uint8Array(bytes));
      return { success: true };
    } catch (e) {
      return { success: false, message: e.message };
    }
  });
}
